taimmk/robok-bipedal/docs/images/addition/111.png

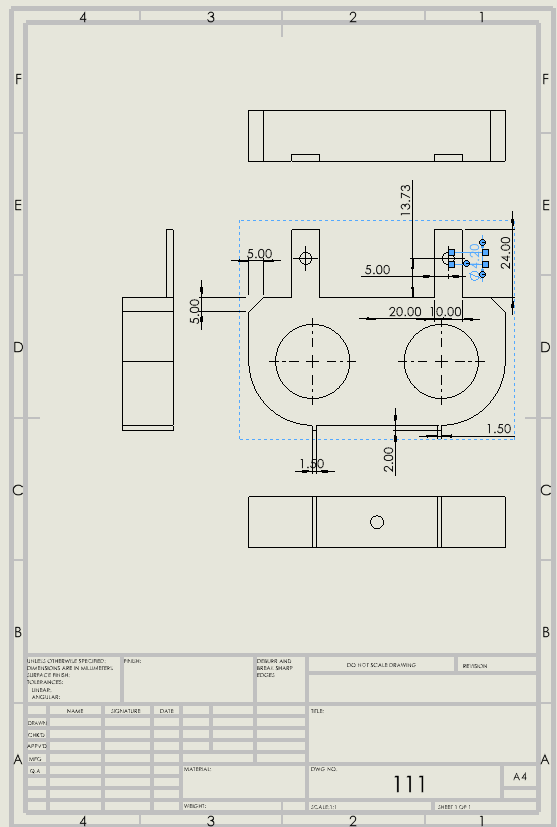
docs/images/addition/111.png
