taimmk/robok-bipedal/docs/images/addition/222.png

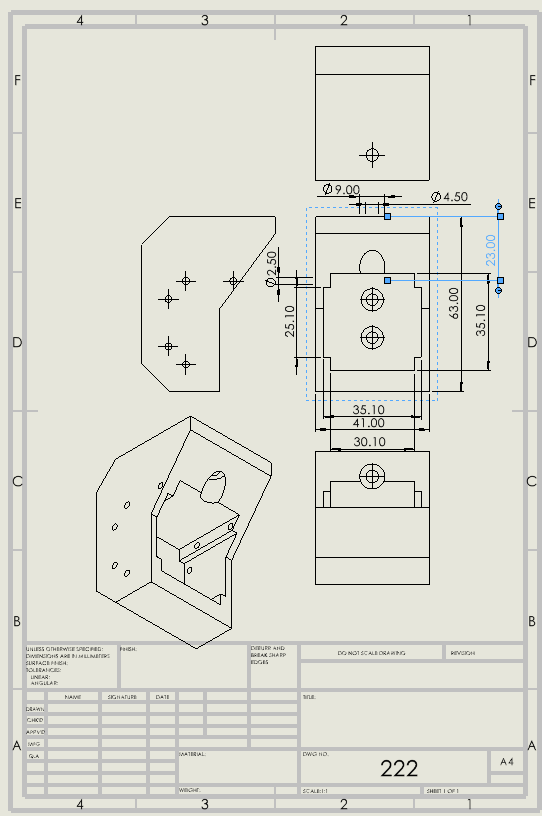
docs/images/addition/222.png
