taimmk/robok-bipedal/docs/images/addition/333.png

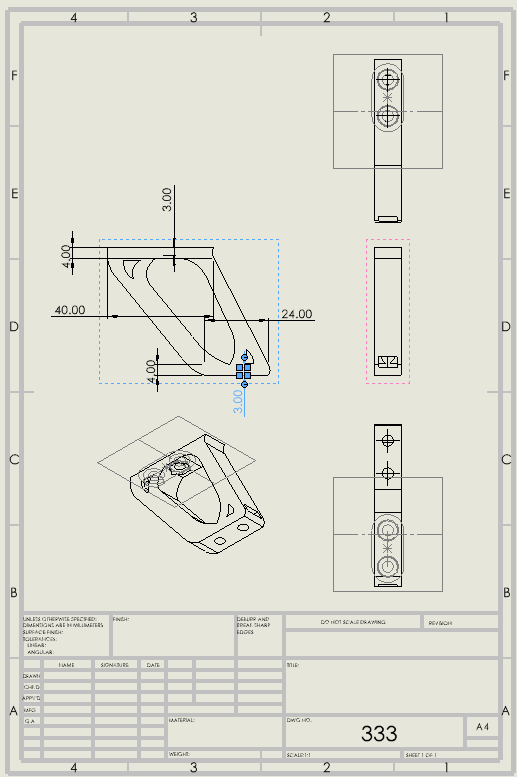
docs/images/addition/333.png
