taimmk/robok-bipedal/docs/images/addition/444.png

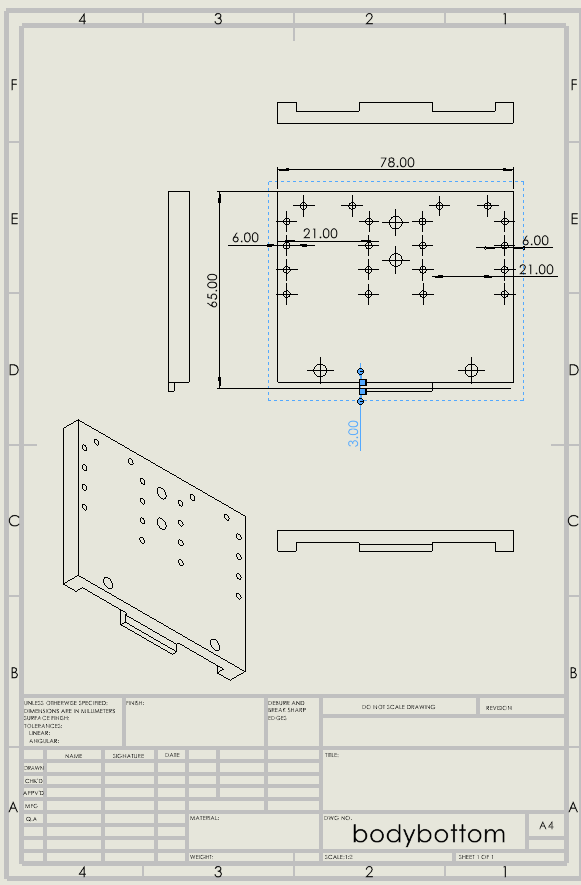
docs/images/addition/444.png
