taimmk/robok-bipedal/docs/images/addition/555.png

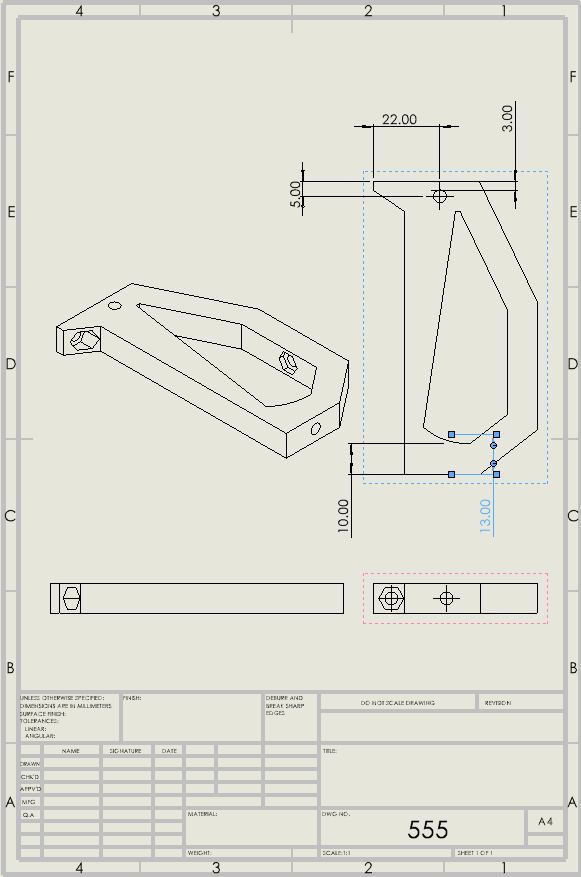
docs/images/addition/555.png
