taimmk/robok-bipedal/docs/images/addition/foot1.png

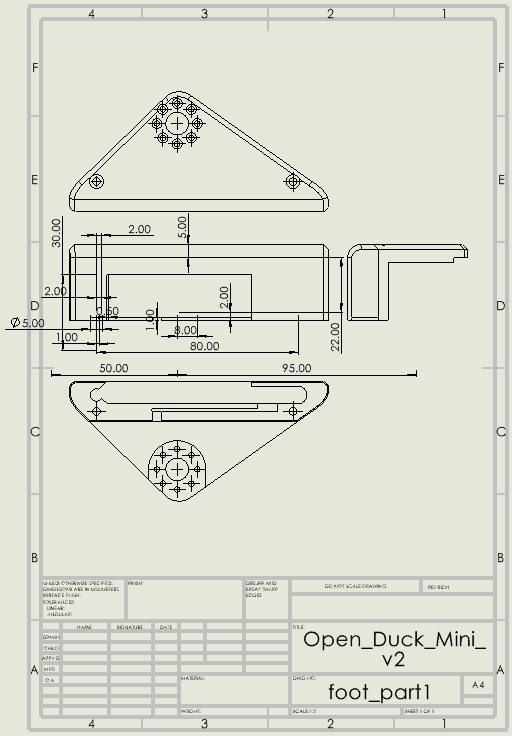
docs/images/addition/foot1.png
