taimmk/robok-bipedal/docs/images/addition/foot2.png

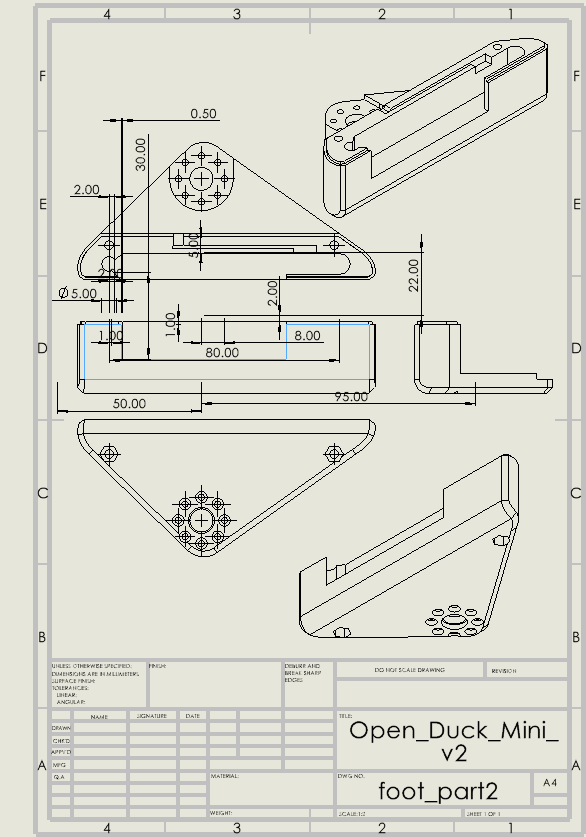
docs/images/addition/foot2.png
