taimmk/robok-bipedal/docs/images/addition/footbot.png

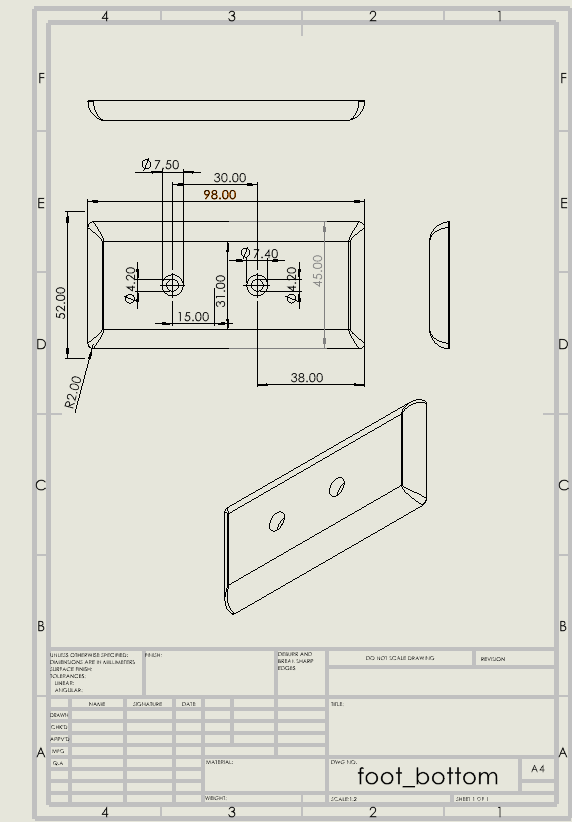
docs/images/addition/footbot.png
