taimmk/robok-bipedal/docs/images/addition/hipallined.png

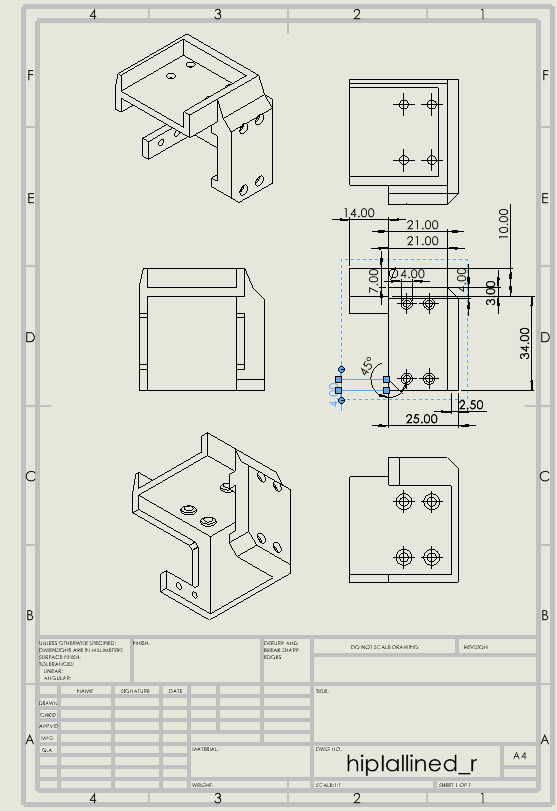
docs/images/addition/hipallined.png
