taimmk/robok-bipedal/docs/images/addition/hipII.png

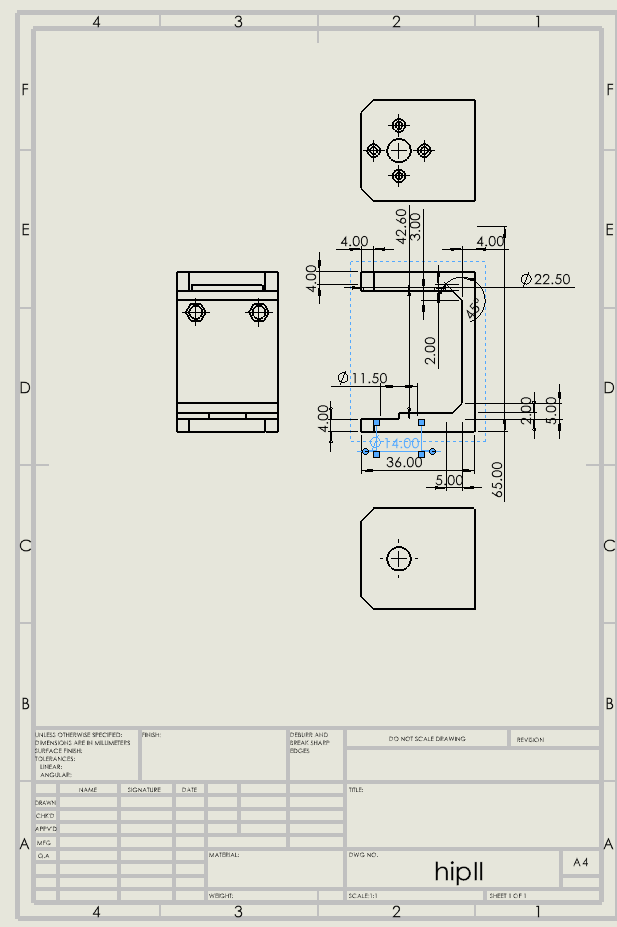
docs/images/addition/hipII.png
