taimmk/robok-bipedal/docs/images/addition/hiproll.png

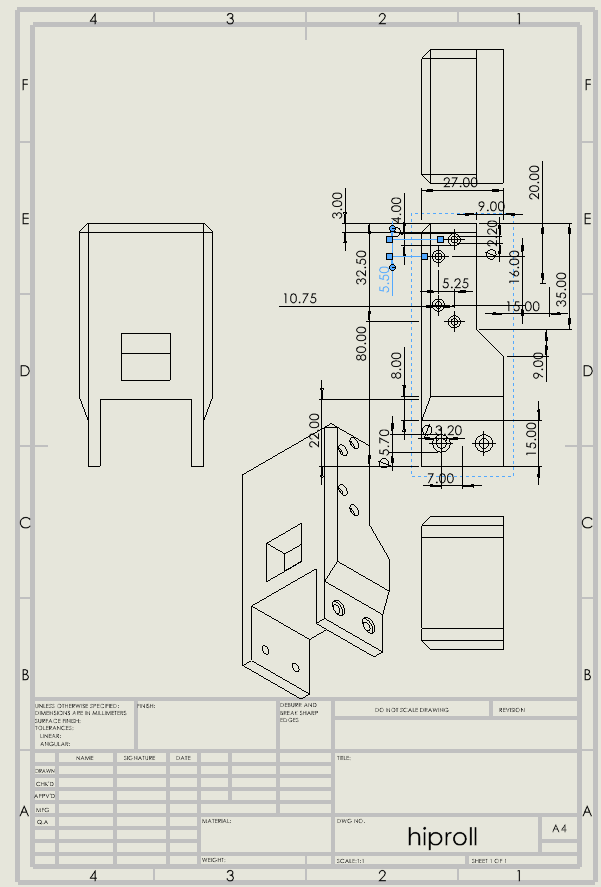
docs/images/addition/hiproll.png
