taimmk/robok-bipedal/docs/images/addition/link.png

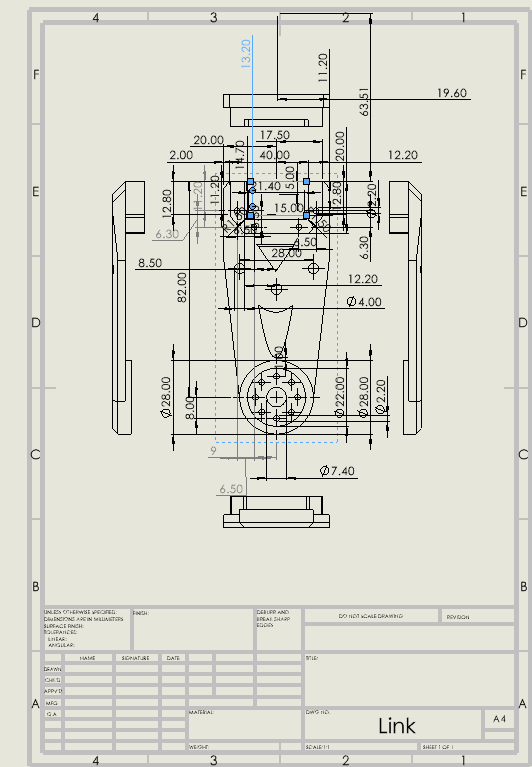
docs/images/addition/link.png
