taimmk/robok-bipedal/docs/images/addition/linkII.png

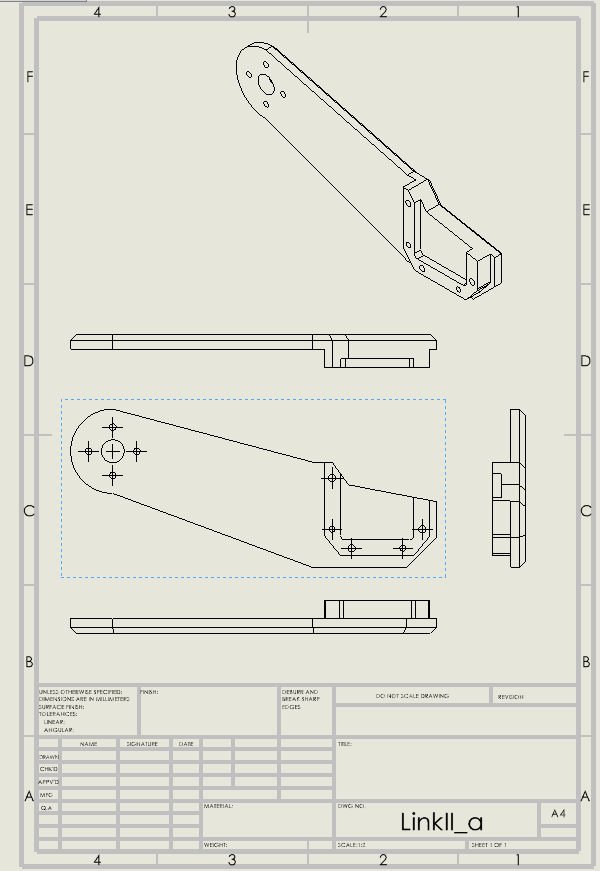
docs/images/addition/linkII.png
