taimmk/robok-bipedal/docs/images/addition/nick.png

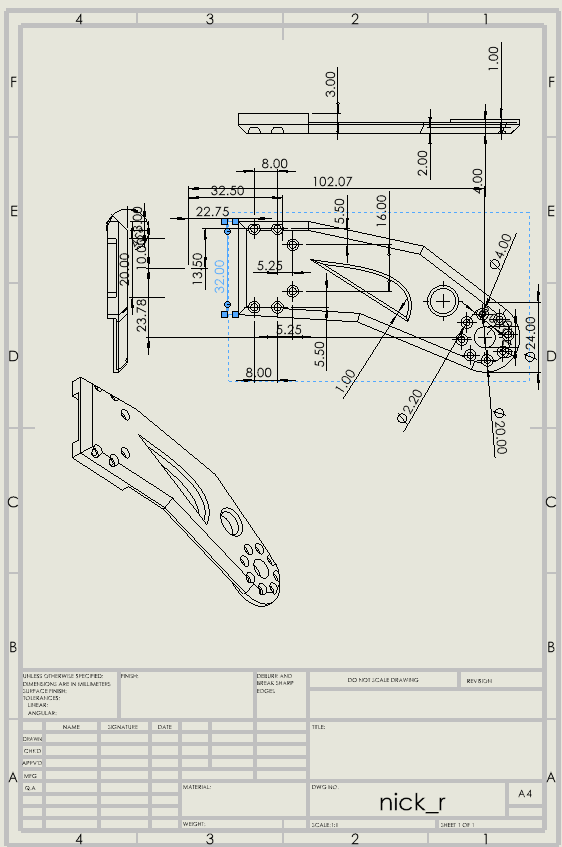
docs/images/addition/nick.png
