taimmk/robok-bipedal/docs/images/addition/nickroll.png

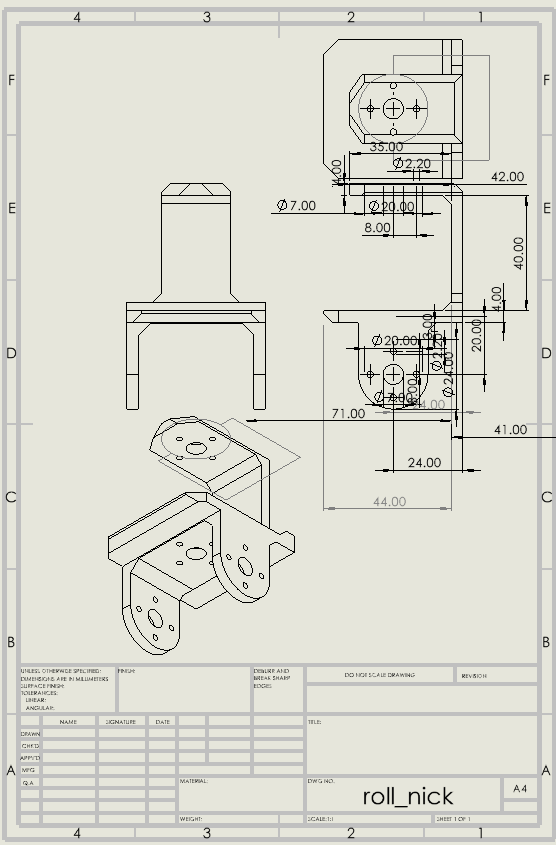
docs/images/addition/nickroll.png
