taimmk/robok-bipedal/docs/images/addition/rollertop.png

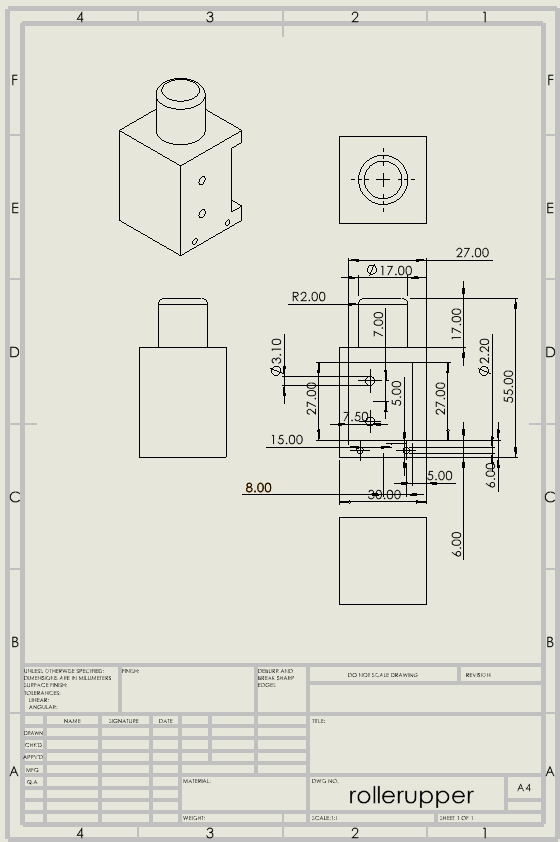
docs/images/addition/rollertop.png
