taimmk/robok-bipedal/docs/images/ANSYS/foot_modal.png

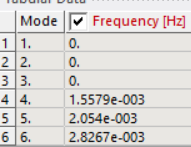
docs/images/ANSYS/foot_modal.png
