taimmk/robok-bipedal/docs/images/ANSYS/foot_optemize.png

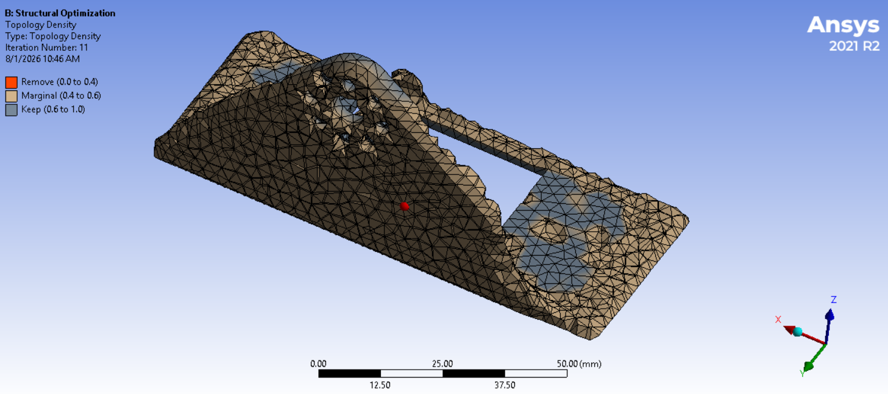
docs/images/ANSYS/foot_optemize.png
