taimmk/robok-bipedal/docs/images/ANSYS/foot_react.png

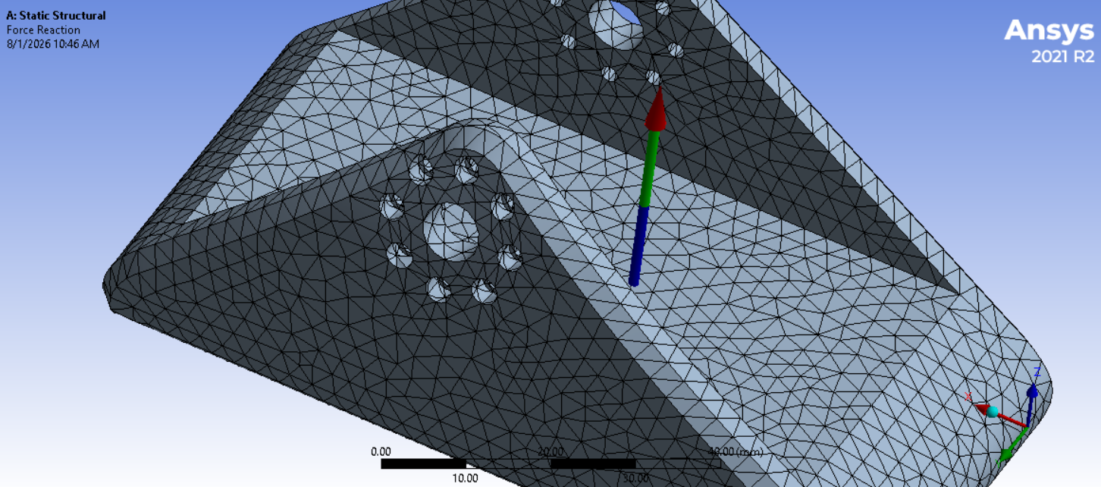
docs/images/ANSYS/foot_react.png
