taimmk/robok-bipedal/docs/images/ANSYS/foot_strain.png

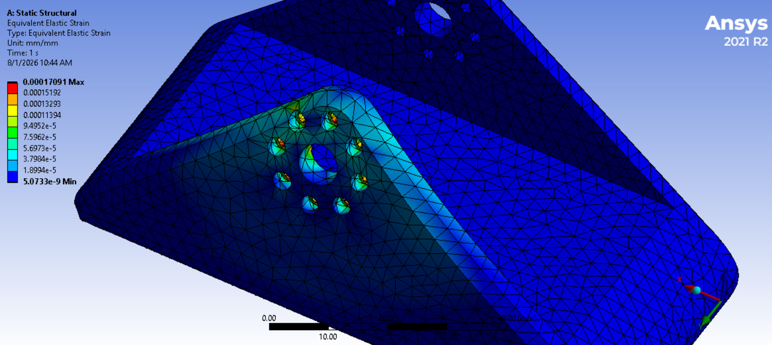
docs/images/ANSYS/foot_strain.png
