taimmk/robok-bipedal/docs/images/ANSYS/foot_totaldeformation.png

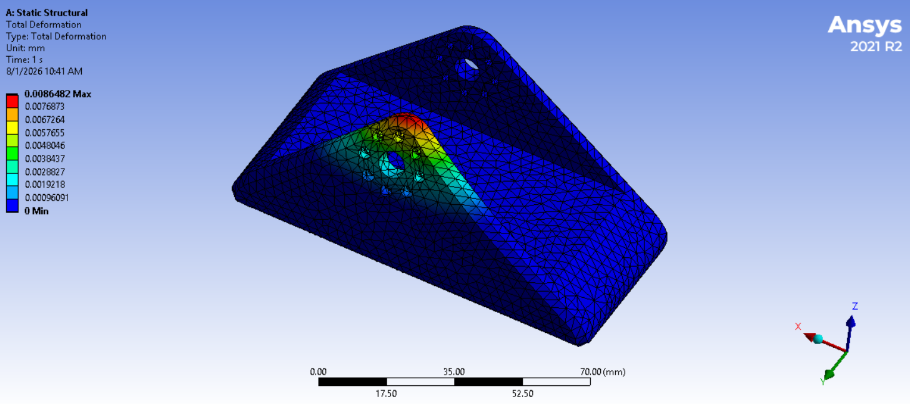
docs/images/ANSYS/foot_totaldeformation.png
