taimmk/robok-bipedal/docs/images/ANSYS/hiproll_modal.png

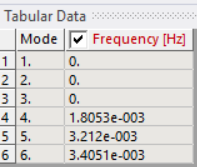
docs/images/ANSYS/hiproll_modal.png
