taimmk/robok-bipedal/docs/images/ANSYS/hiproll_optemize.png

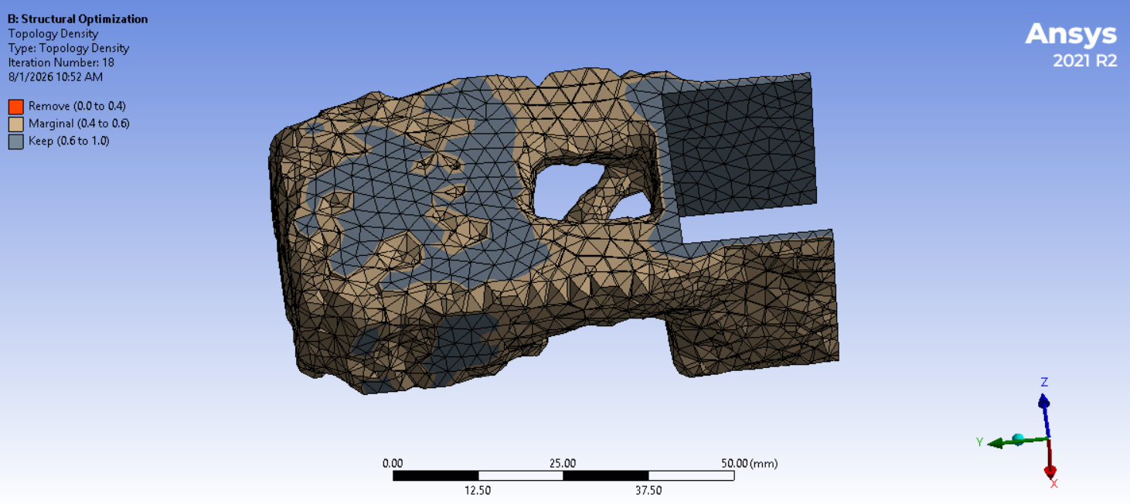
docs/images/ANSYS/hiproll_optemize.png
