taimmk/robok-bipedal/docs/images/ANSYS/hiproll_strain.png

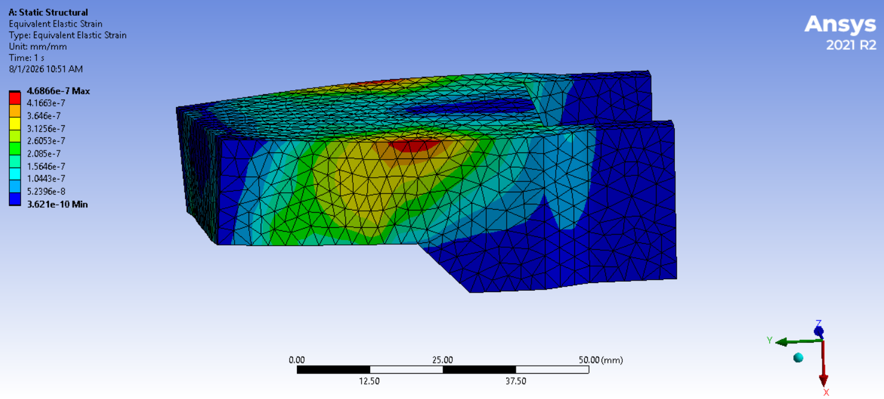
docs/images/ANSYS/hiproll_strain.png
