taimmk/robok-bipedal/docs/images/ANSYS/hiproll_totaldeformation.png

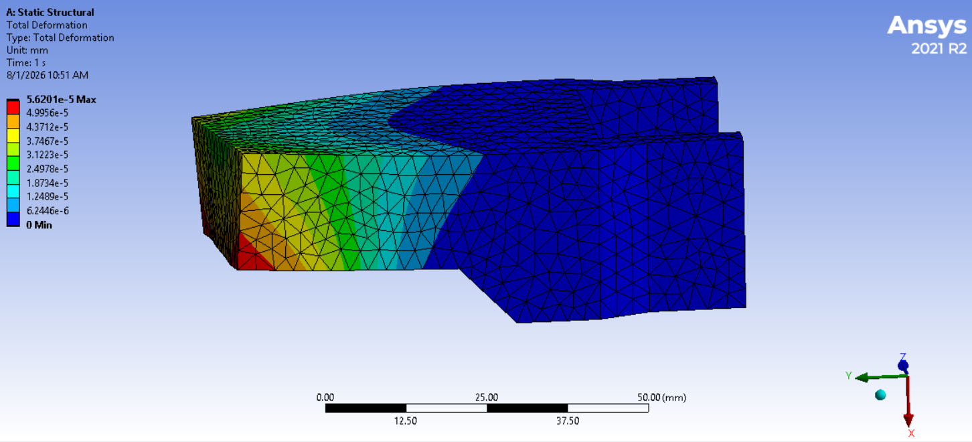
docs/images/ANSYS/hiproll_totaldeformation.png
