taimmk/robok-bipedal/docs/images/ANSYS/linki_optemize.png

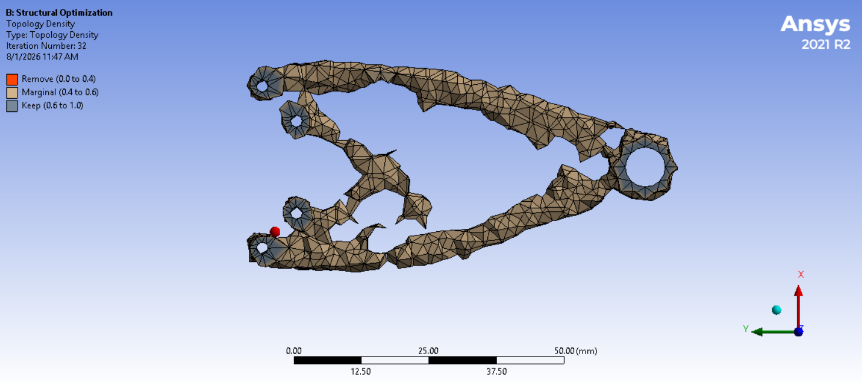
docs/images/ANSYS/linki_optemize.png
