taimmk/robok-bipedal/docs/images/ANSYS/linki_react.png

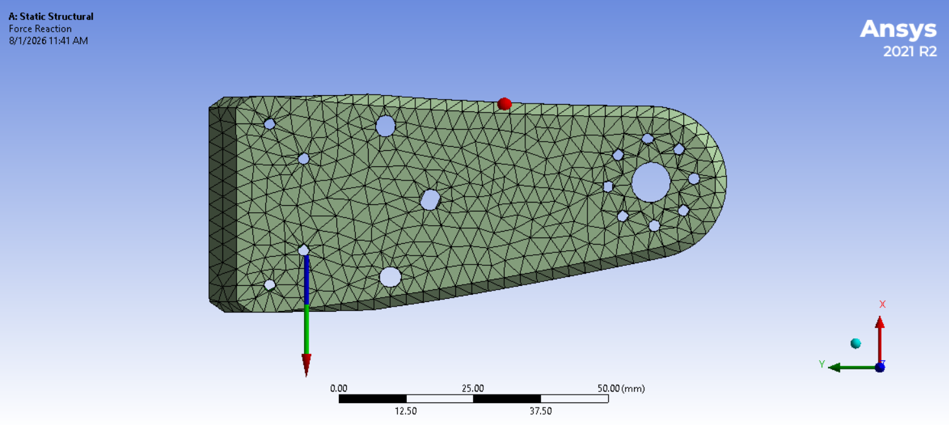
docs/images/ANSYS/linki_react.png
