taimmk/robok-bipedal/docs/images/ANSYS/linki_strain.png

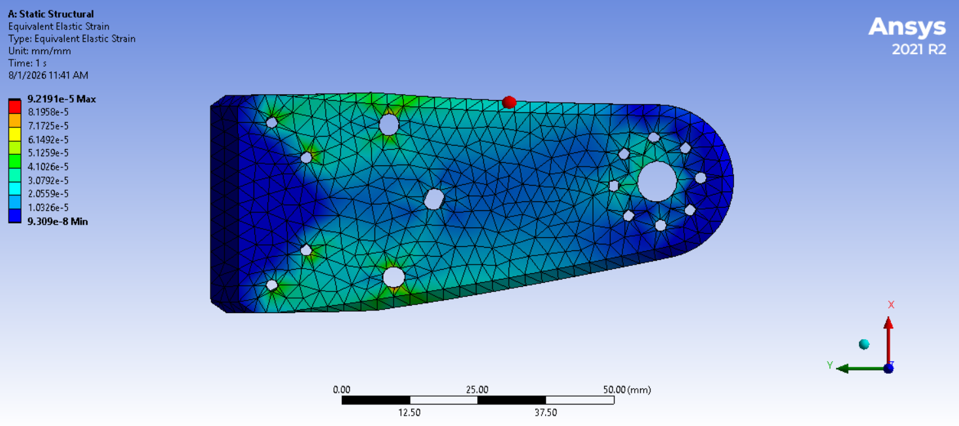
docs/images/ANSYS/linki_strain.png
