taimmk/robok-bipedal/docs/images/ANSYS/linki_totaldeformation.png

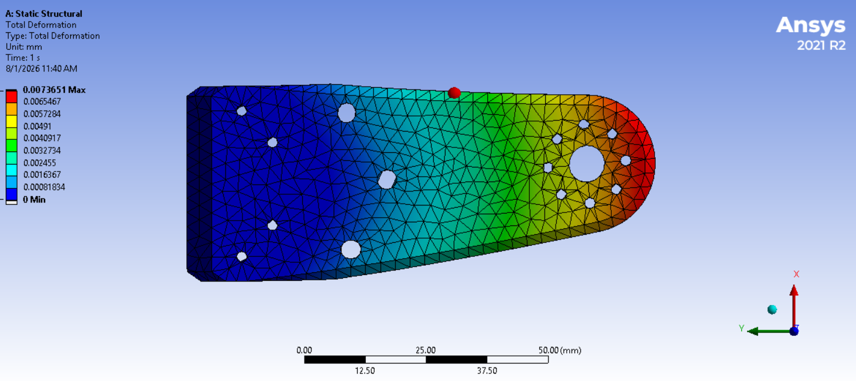
docs/images/ANSYS/linki_totaldeformation.png
