taimmk/robok-bipedal/docs/images/ANSYS/linkii_optemize.png

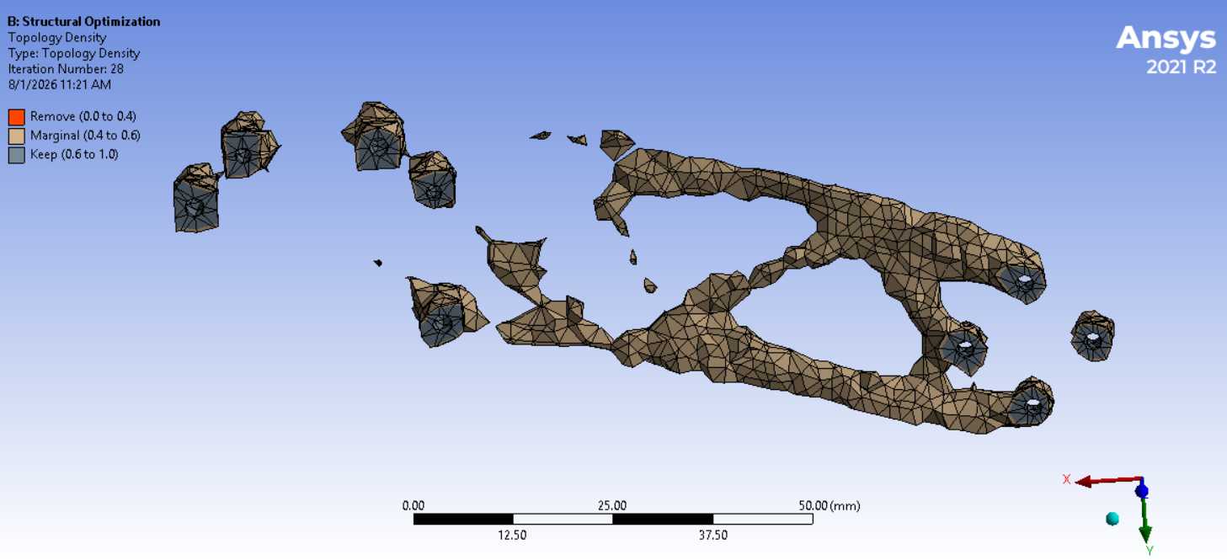
docs/images/ANSYS/linkii_optemize.png
