taimmk/robok-bipedal/docs/images/ANSYS/linkii_react.png

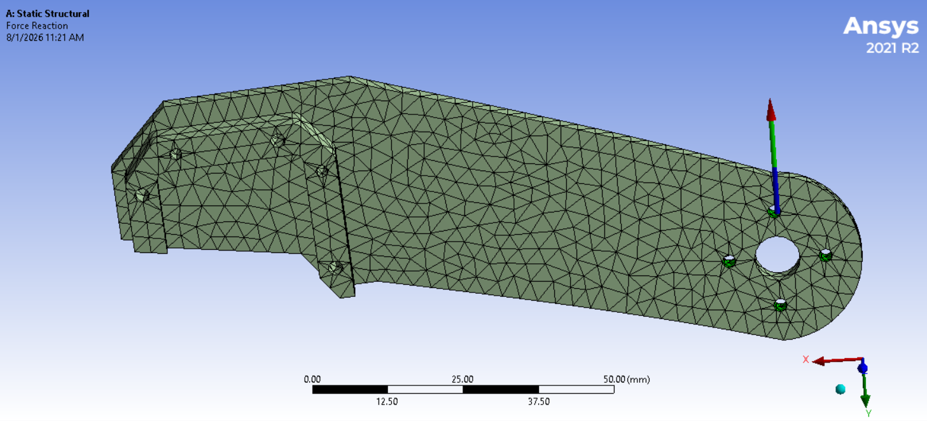
docs/images/ANSYS/linkii_react.png
