taimmk/robok-bipedal/docs/images/ANSYS/linkii_strain.png

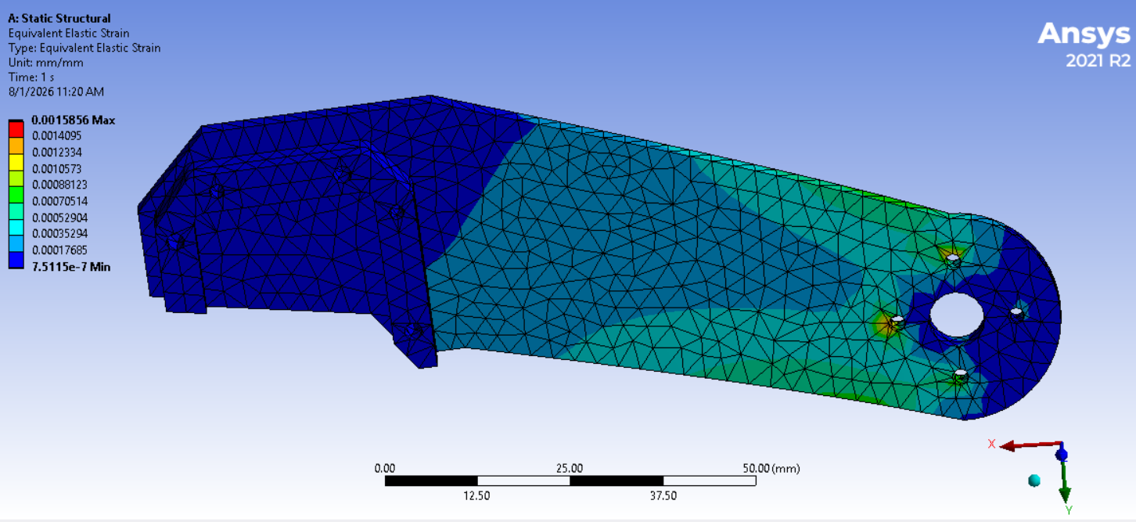
docs/images/ANSYS/linkii_strain.png
