taimmk/robok-bipedal/docs/images/ANSYS/linkii_totaldeformation.png

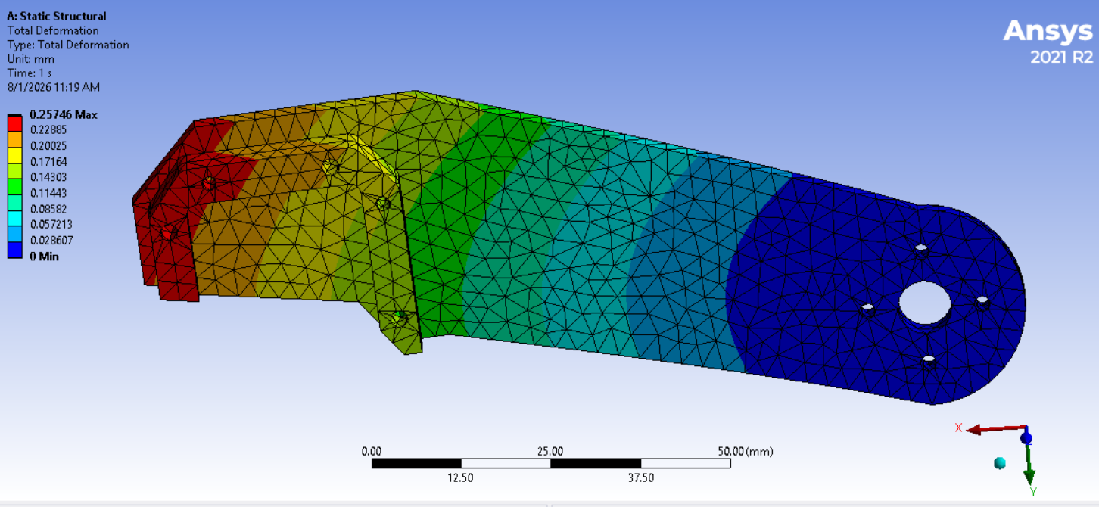
docs/images/ANSYS/linkii_totaldeformation.png
