taimmk/robok-bipedal/docs/images/ANSYS/nick_optemize.png

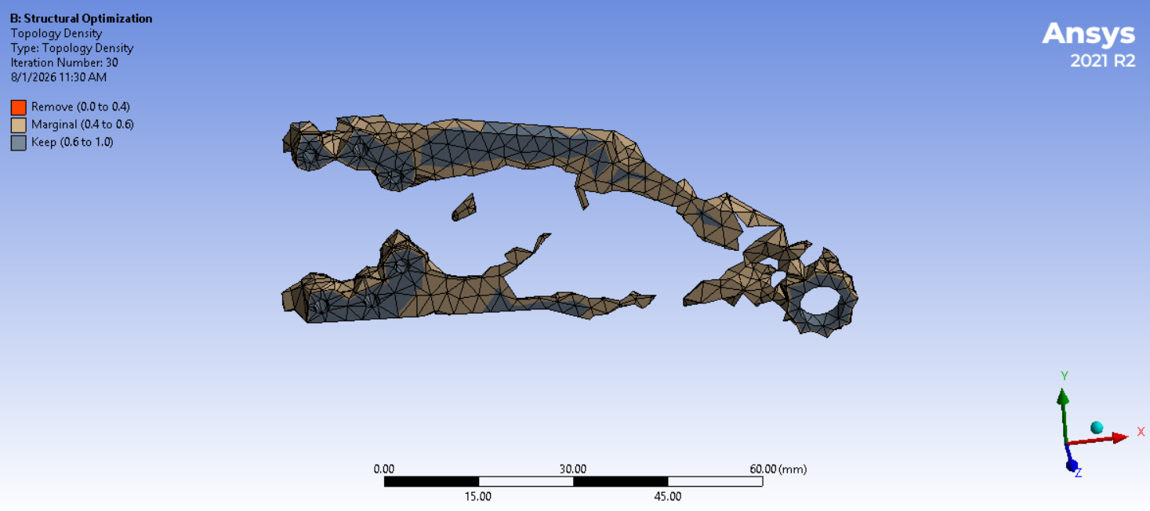
docs/images/ANSYS/nick_optemize.png
