taimmk/robok-bipedal/docs/images/ANSYS/nick_react.png

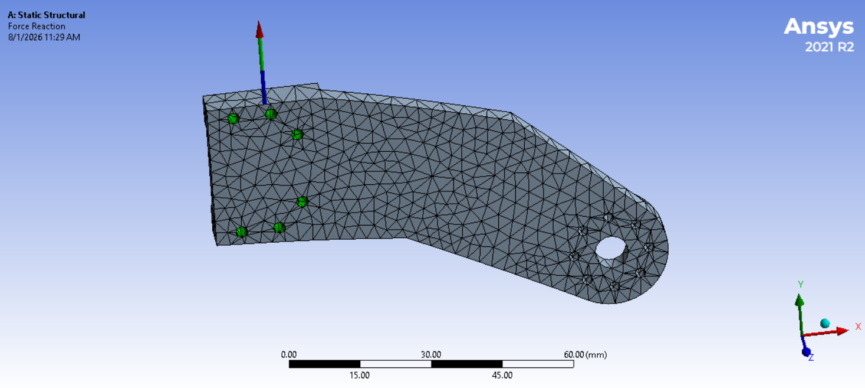
docs/images/ANSYS/nick_react.png
