taimmk/robok-bipedal/docs/images/ANSYS/nick_strain.png

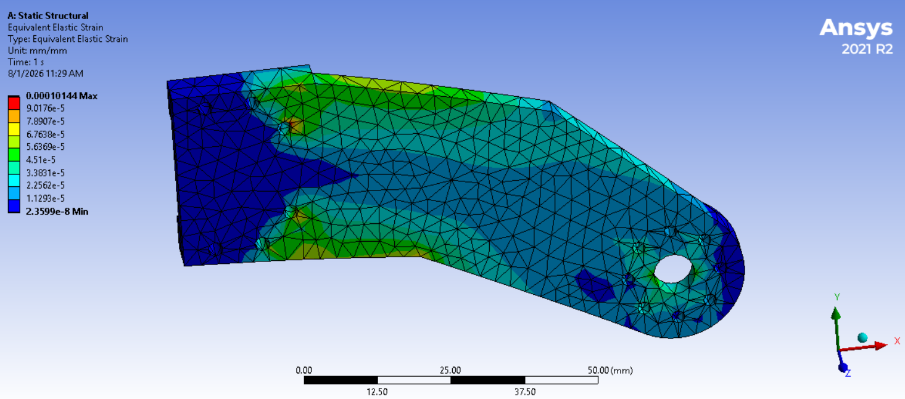
docs/images/ANSYS/nick_strain.png
