taimmk/robok-bipedal/docs/images/ANSYS/nick_totaldeformation.png

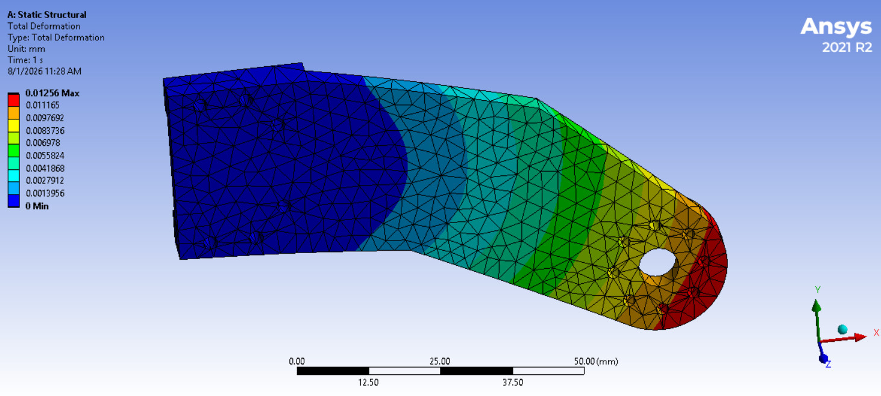
docs/images/ANSYS/nick_totaldeformation.png
