taimmk/robok-bipedal/docs/images/configuration.png

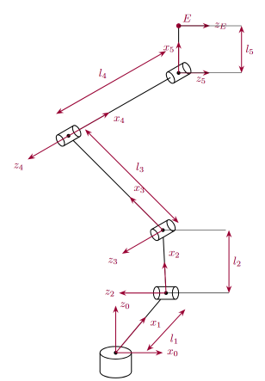
docs/images/configuration.png
