taimmk/robok-bipedal/docs/images/fkmat.png

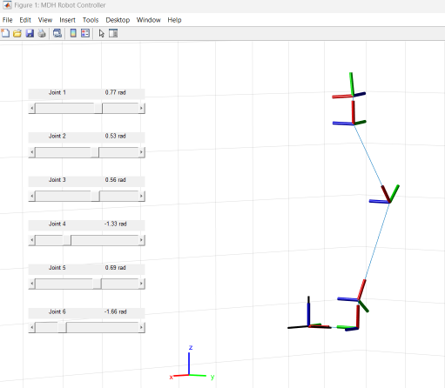
docs/images/fkmat.png
