taimmk/robok-bipedal/docs/images/funcitonsanswhy.png

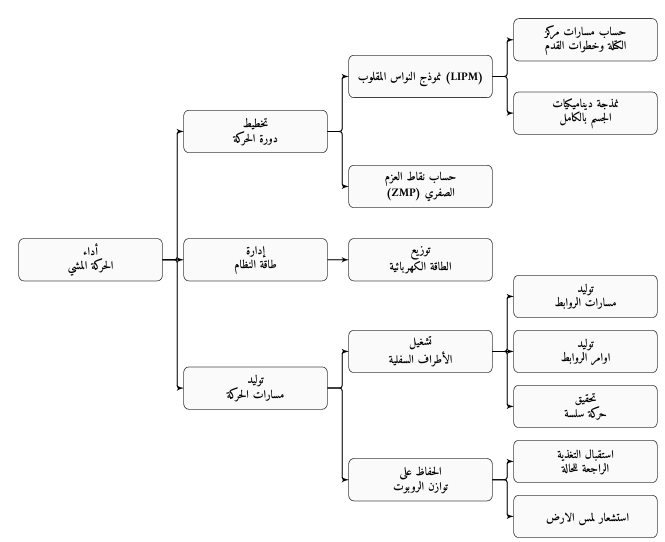
docs/images/funcitonsanswhy.png
