taimmk/robok-bipedal/docs/images/hornsdiagrams.png

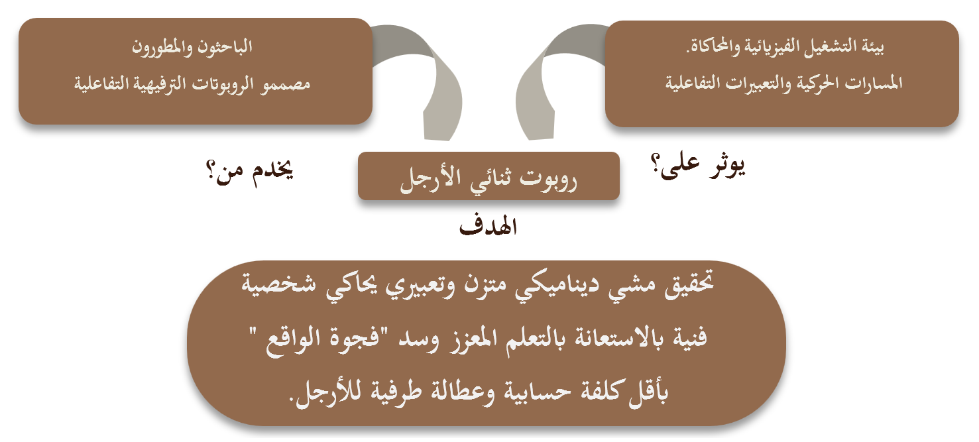
docs/images/hornsdiagrams.png
