taimmk/robok-bipedal/docs/images/inputoutput01.png

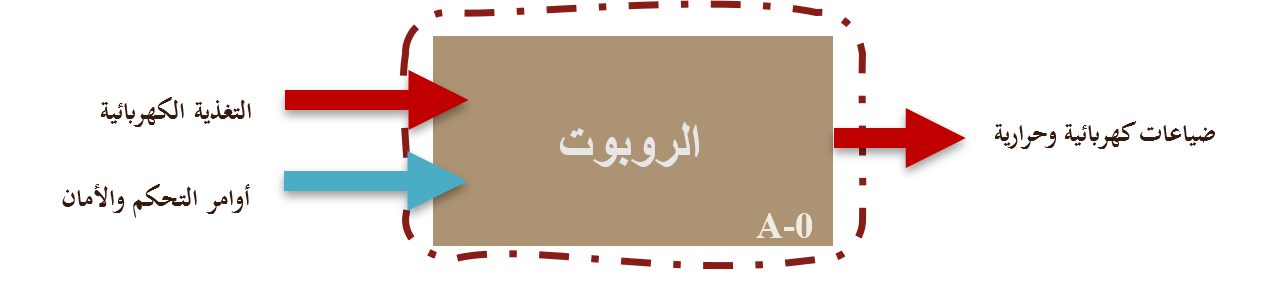
docs/images/inputoutput01.png
