taimmk/robok-bipedal/docs/images/invkin.png

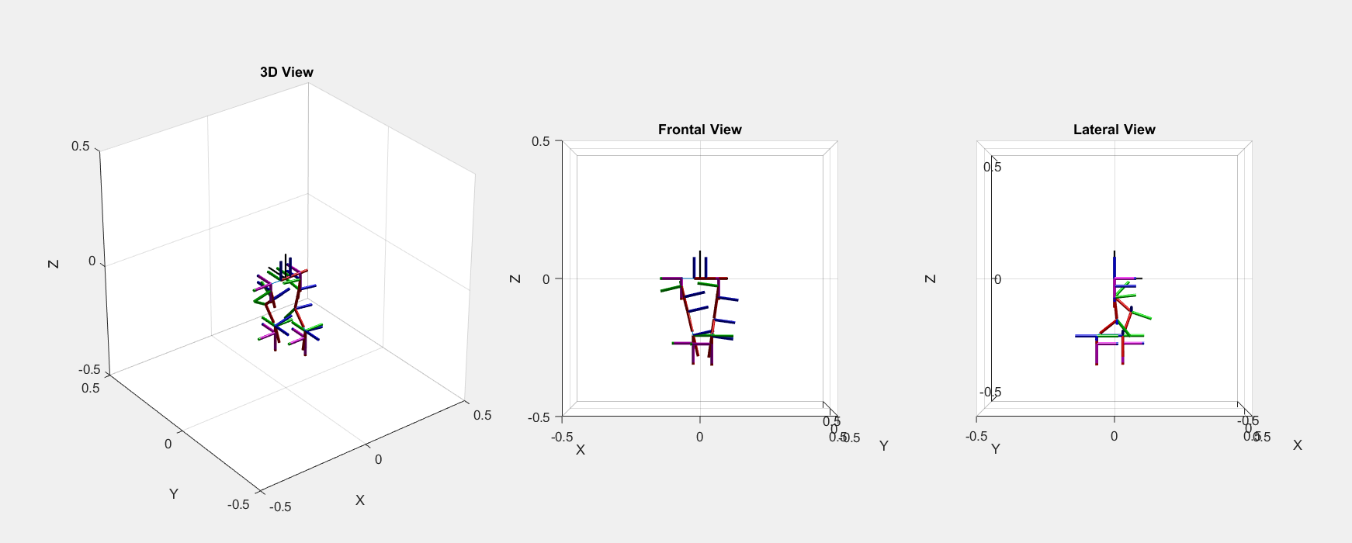
docs/images/invkin.png
