taimmk/robok-bipedal/docs/images/joint1.png

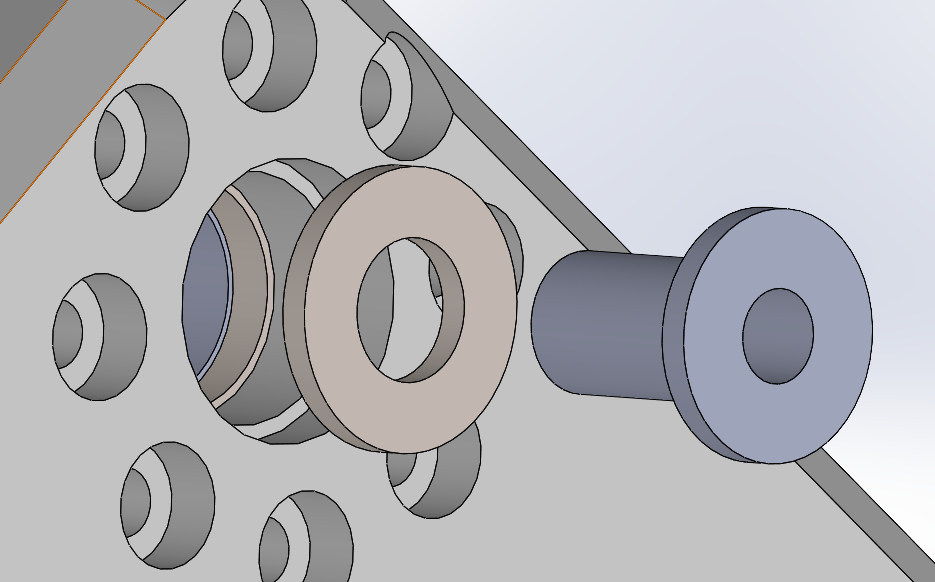
docs/images/joint1.png
