taimmk/robok-bipedal/docs/images/joint2.png

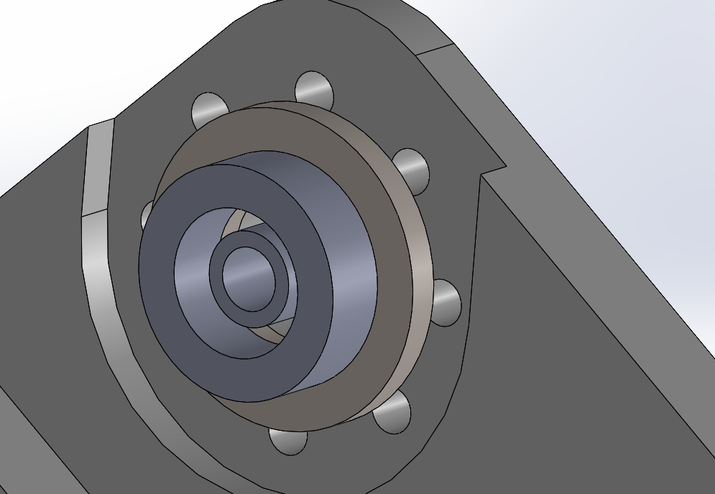
docs/images/joint2.png
