taimmk/robok-bipedal/docs/images/jointax.png

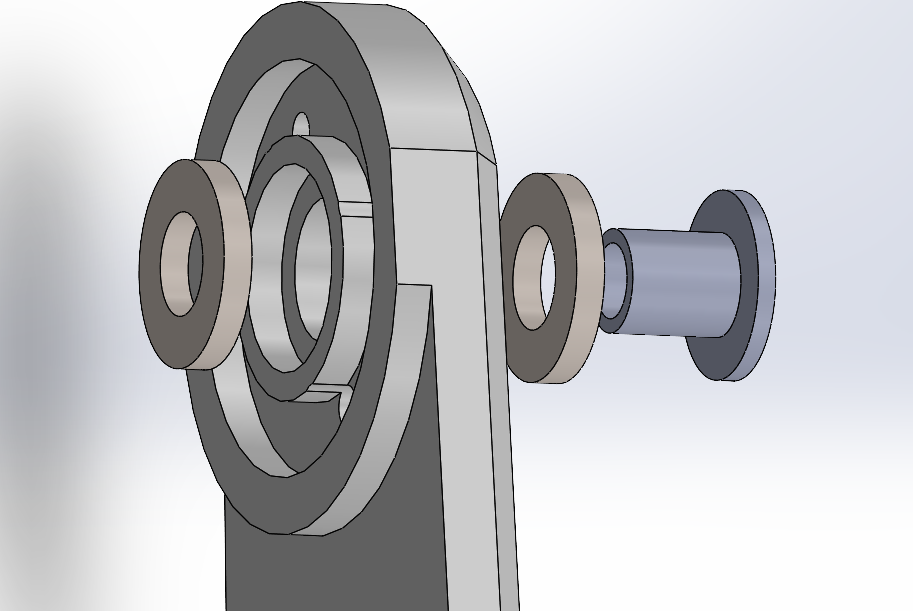
docs/images/jointax.png
