taimmk/robok-bipedal/docs/images/LIPM.png

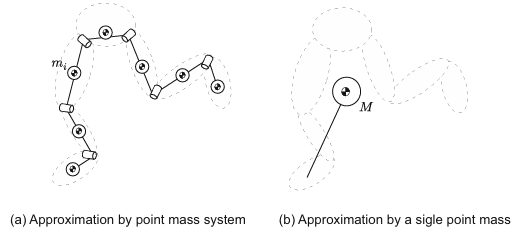
docs/images/LIPM.png
