taimmk/robok-bipedal/docs/images/lipmapp.png

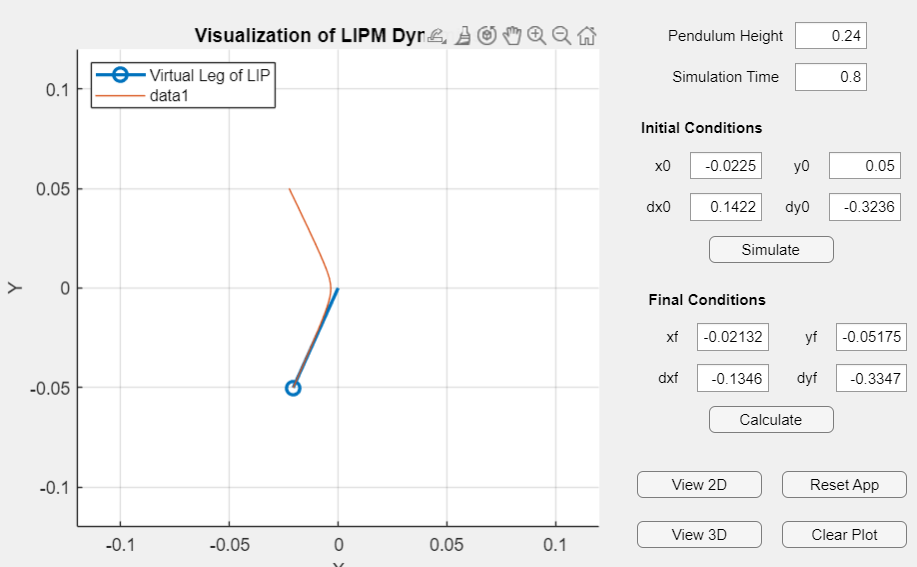
docs/images/lipmapp.png
