taimmk/robok-bipedal/docs/images/lipmoutput.png

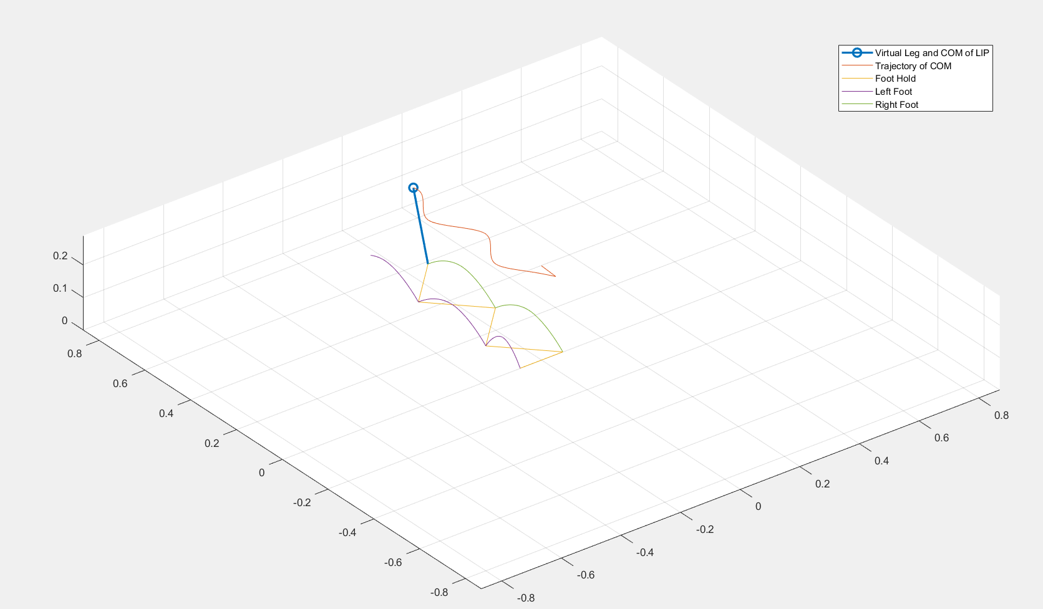
docs/images/lipmoutput.png
