taimmk/robok-bipedal/docs/images/matlabdiagram.png

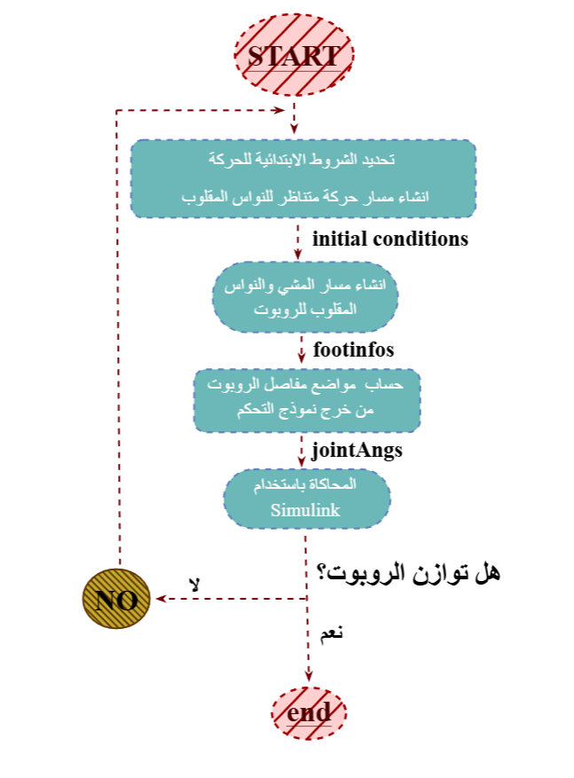
docs/images/matlabdiagram.png
