taimmk/robok-bipedal/docs/images/mpc.jpg

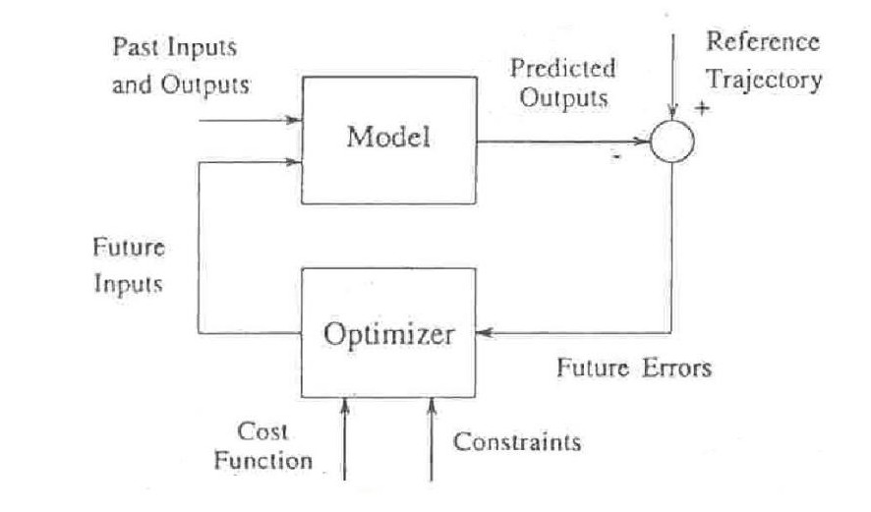
docs/images/mpc.jpg
