taimmk/robok-bipedal/docs/images/orbital_energy.png

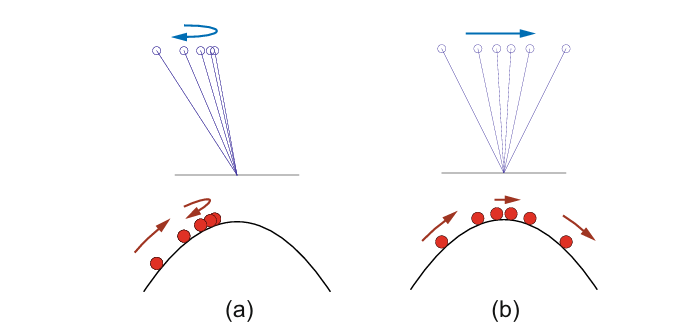
docs/images/orbital_energy.png
