taimmk/robok-bipedal/docs/images/outaffect.png

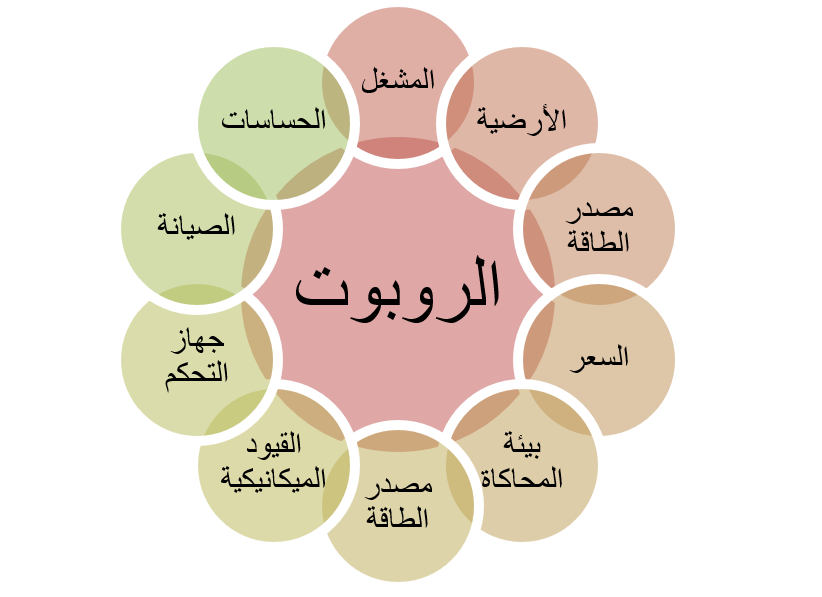
docs/images/outaffect.png
