taimmk/robok-bipedal/docs/images/PCB/communication_2d.png

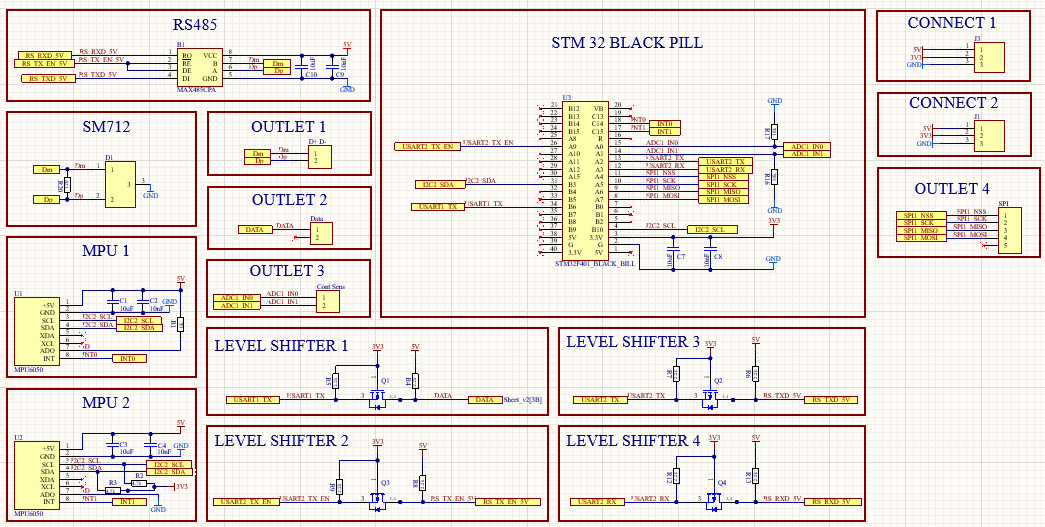
docs/images/PCB/communication_2d.png
