taimmk/robok-bipedal/docs/images/PCB/communication_3d.png

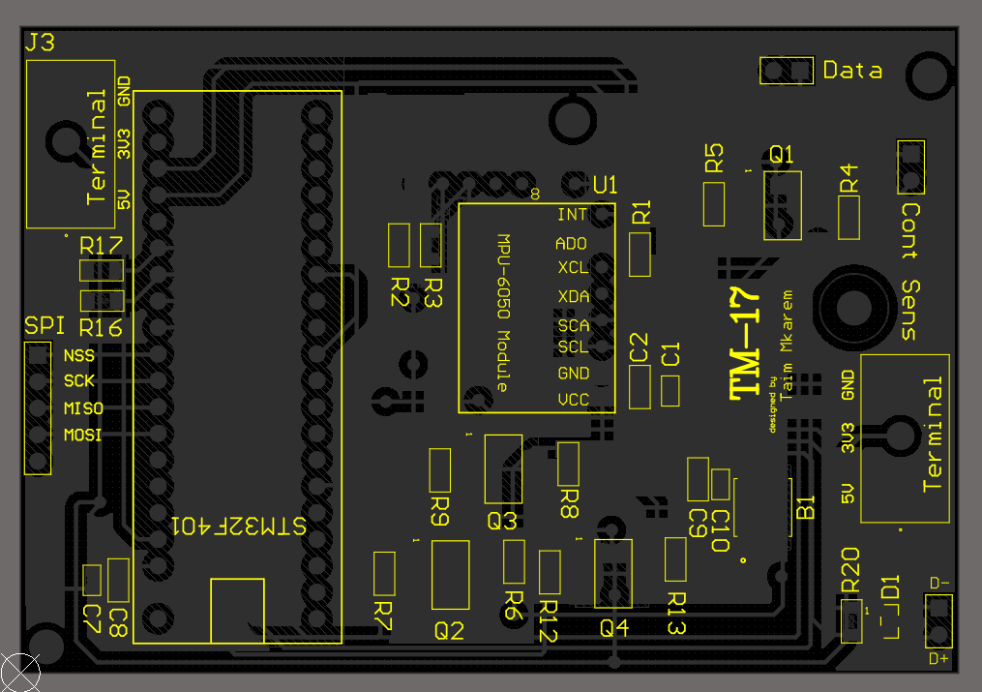
docs/images/PCB/communication_3d.png
