taimmk/robok-bipedal/docs/images/PCB/Gemini_Generated_Image_nam9vcnam9vcnam9.png

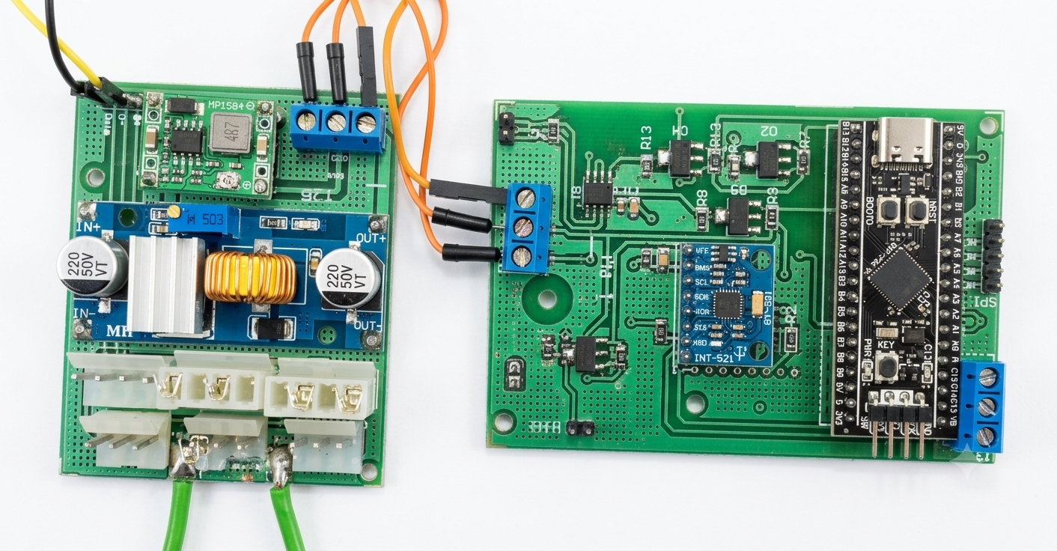
docs/images/PCB/Gemini_Generated_Image_nam9vcnam9vcnam9.png
