taimmk/robok-bipedal/docs/images/PCB/power_2d.png

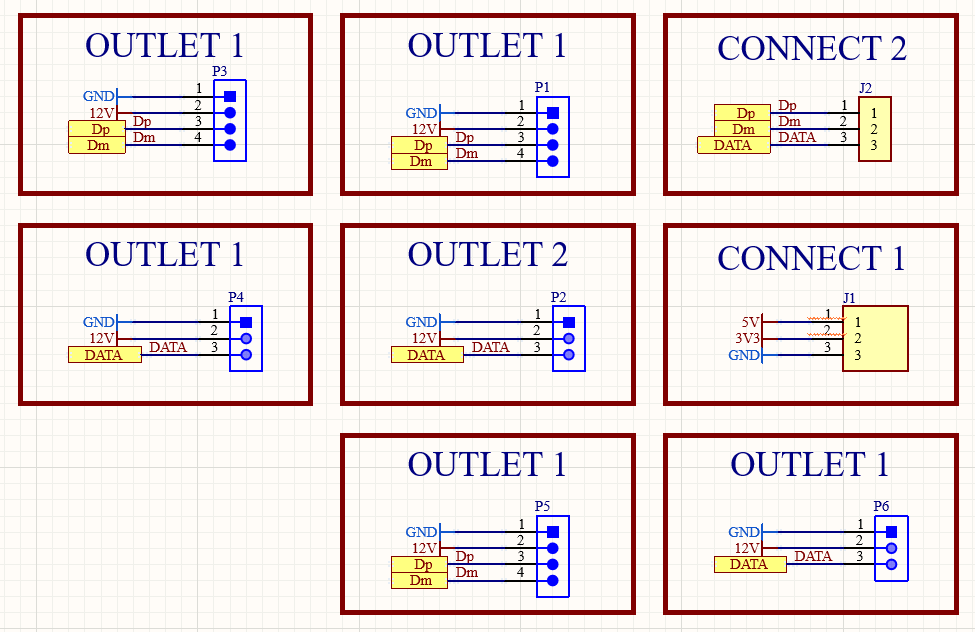
docs/images/PCB/power_2d.png
