taimmk/robok-bipedal/docs/images/PCB/power_3d.png

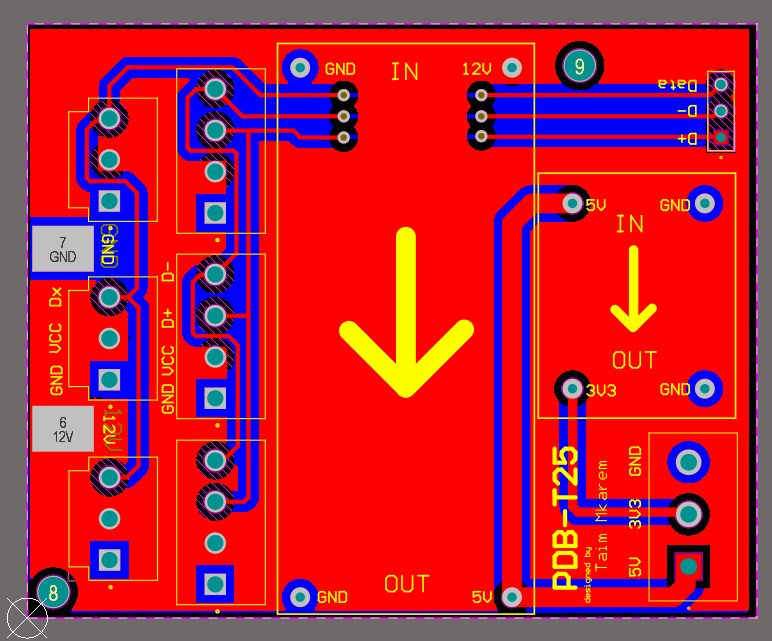
docs/images/PCB/power_3d.png
