taimmk/robok-bipedal/docs/images/PCB/real.jpg

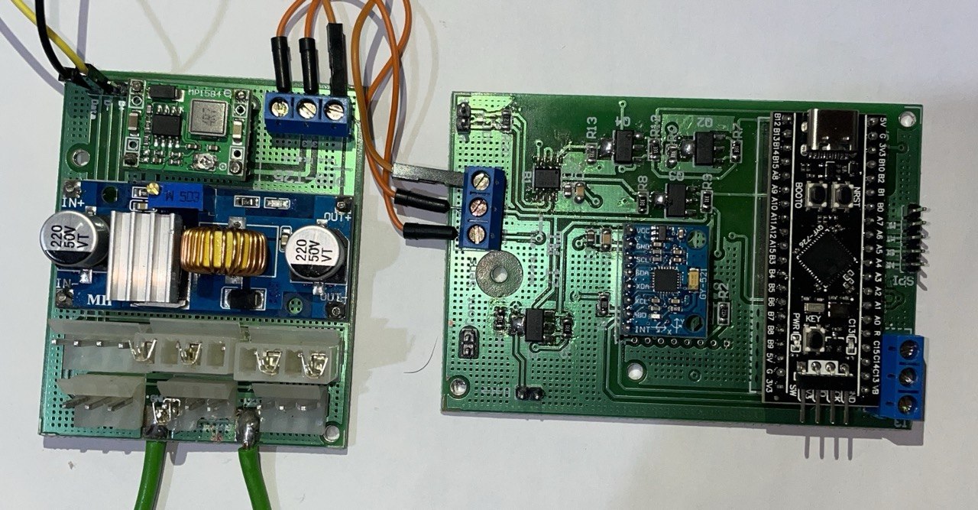
docs/images/PCB/real.jpg
