taimmk/robok-bipedal/docs/images/real.png

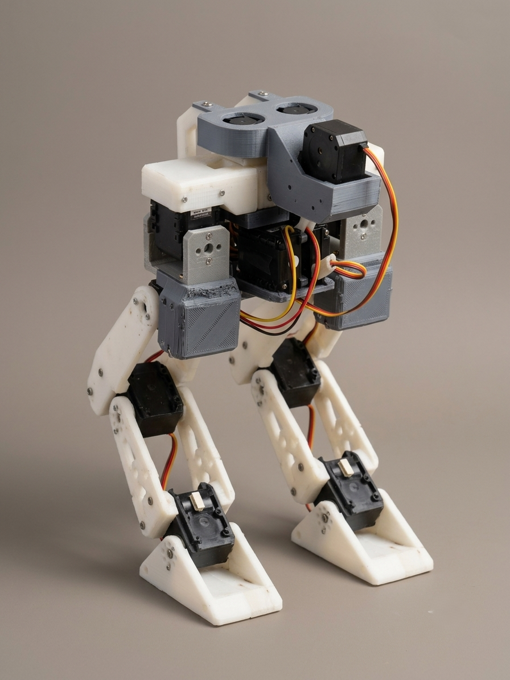
docs/images/real.png
