taimmk/robok-bipedal/docs/images/realside.png

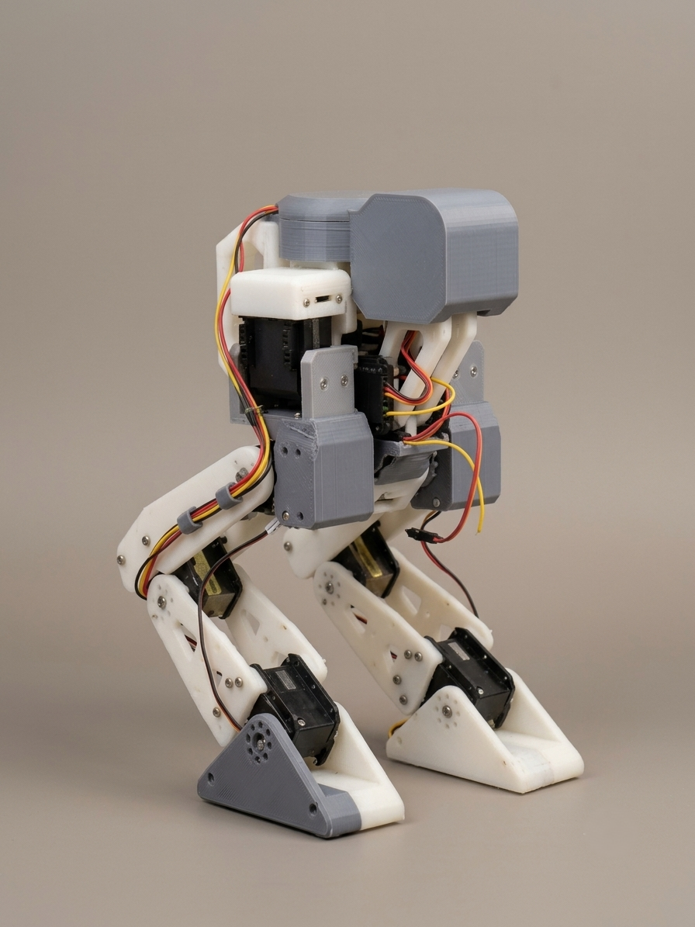
docs/images/realside.png
