taimmk/robok-bipedal/docs/images/rl/feetairtime.png

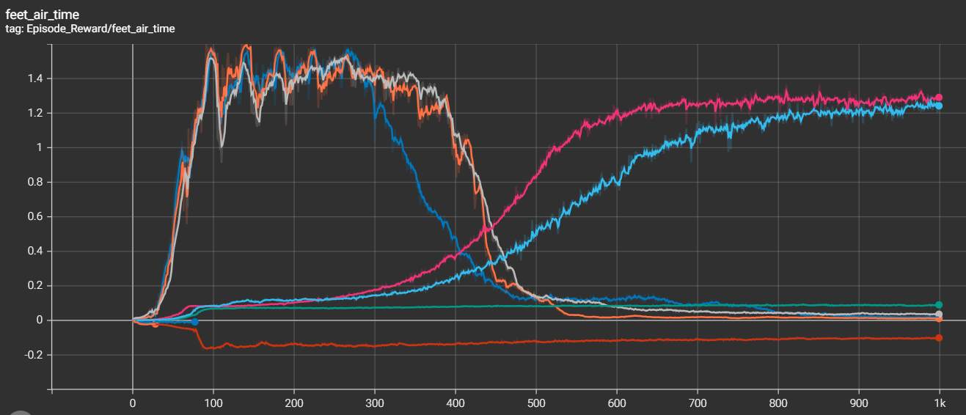
docs/images/rl/feetairtime.png
