taimmk/robok-bipedal/docs/images/rl/learningrate.png

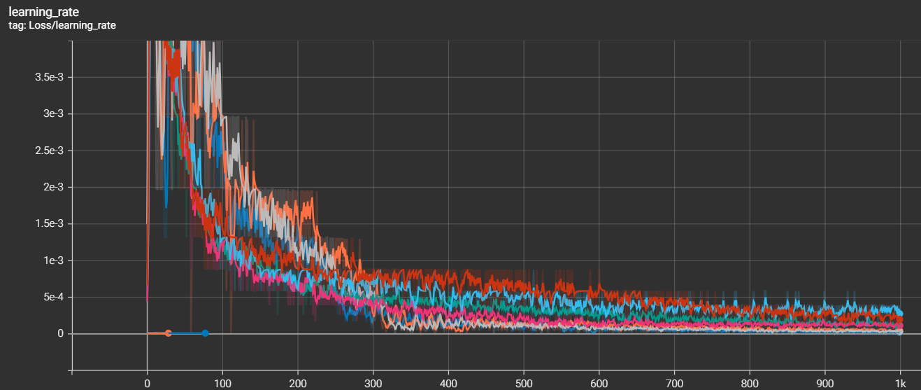
docs/images/rl/learningrate.png
