taimmk/robok-bipedal/docs/images/rl/meanepisodelength.png

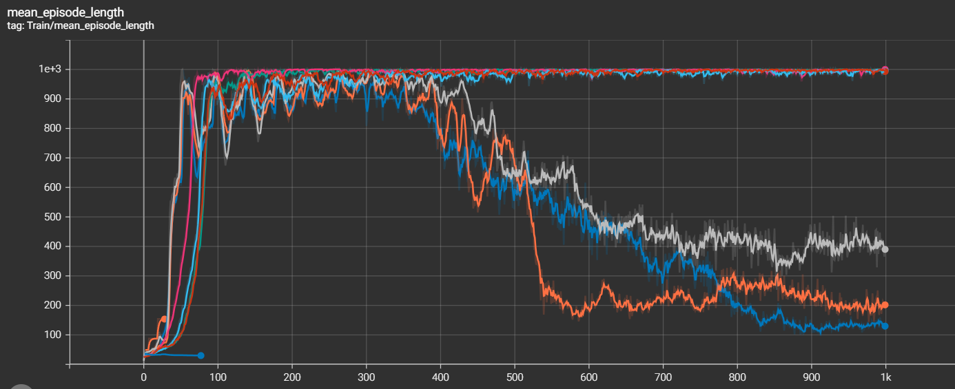
docs/images/rl/meanepisodelength.png
