taimmk/robok-bipedal/docs/images/rl/meanreward.png

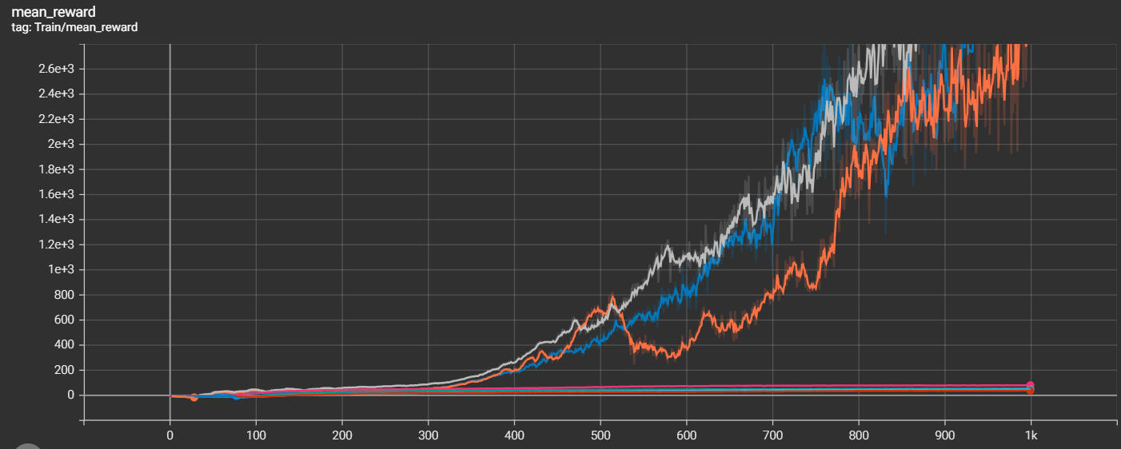
docs/images/rl/meanreward.png
