taimmk/robok-bipedal/docs/images/rl/meanstd.png

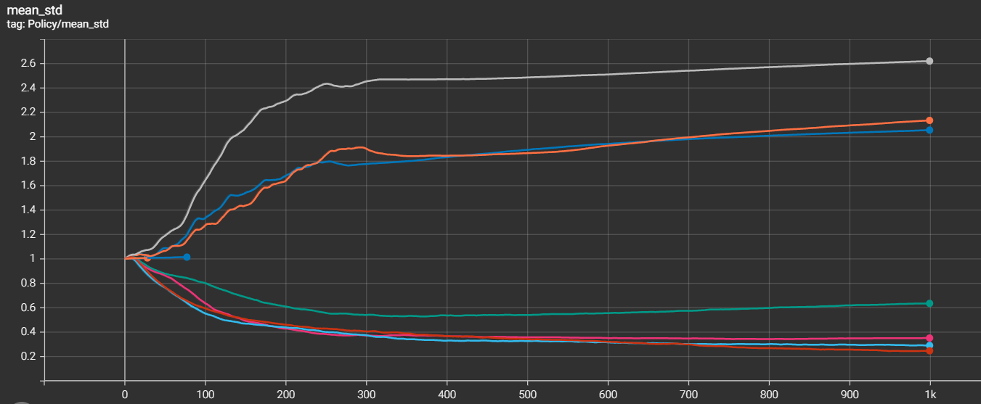
docs/images/rl/meanstd.png
