taimmk/robok-bipedal/docs/images/rl/sucessrate.png

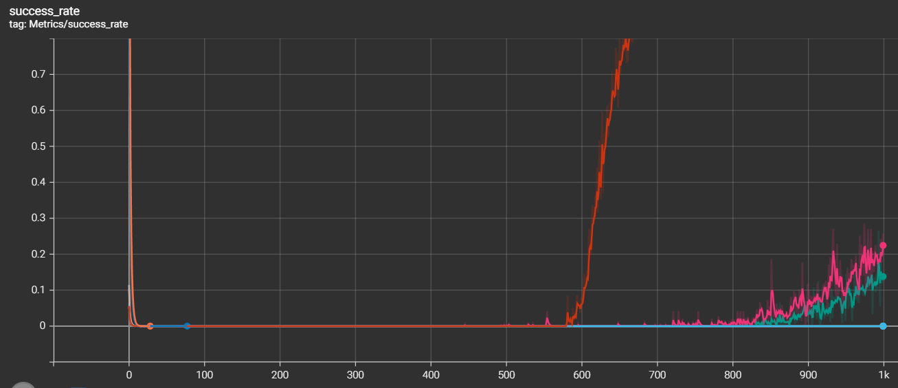
docs/images/rl/sucessrate.png
