taimmk/robok-bipedal/docs/images/rlrsl.png

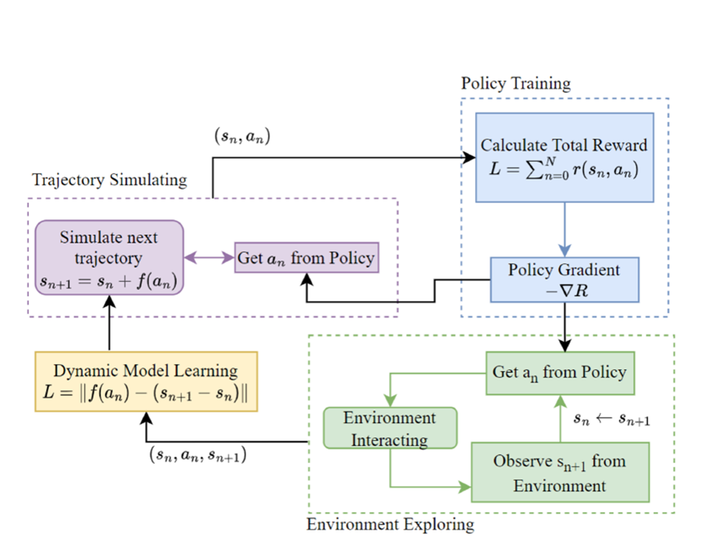
docs/images/rlrsl.png
