taimmk/robok-bipedal/docs/images/robokfront.png

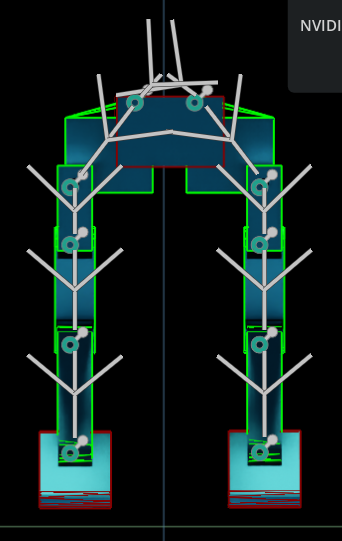
docs/images/robokfront.png
