taimmk/robok-bipedal/docs/images/robokpre.png

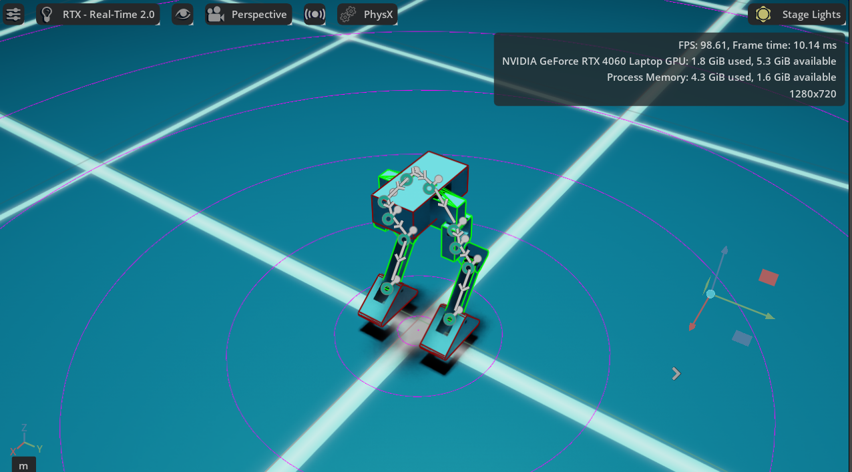
docs/images/robokpre.png
