taimmk/robok-bipedal/docs/images/robokright.png

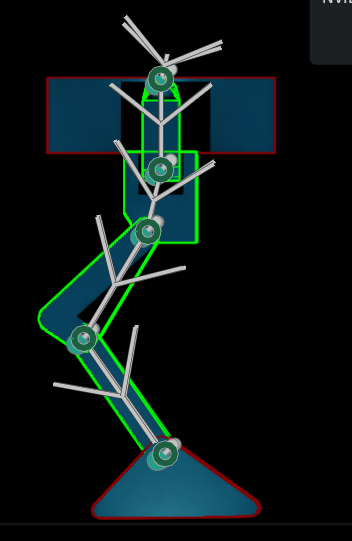
docs/images/robokright.png
