taimmk/robok-bipedal/docs/images/rslrl.png

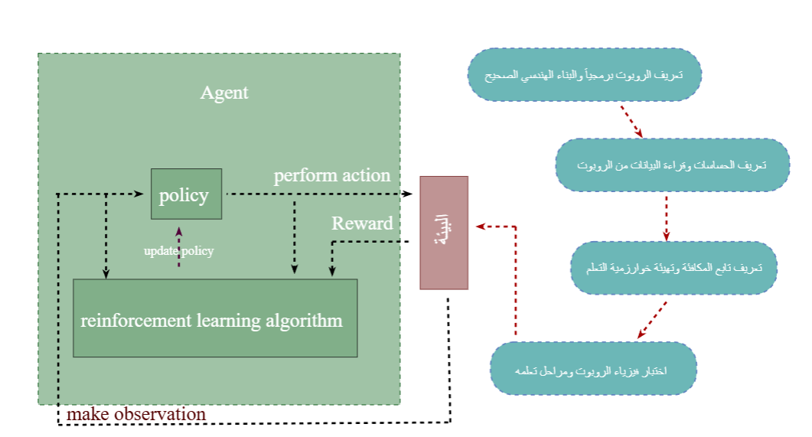
docs/images/rslrl.png
