taimmk/robok-bipedal/docs/images/simulink2.png

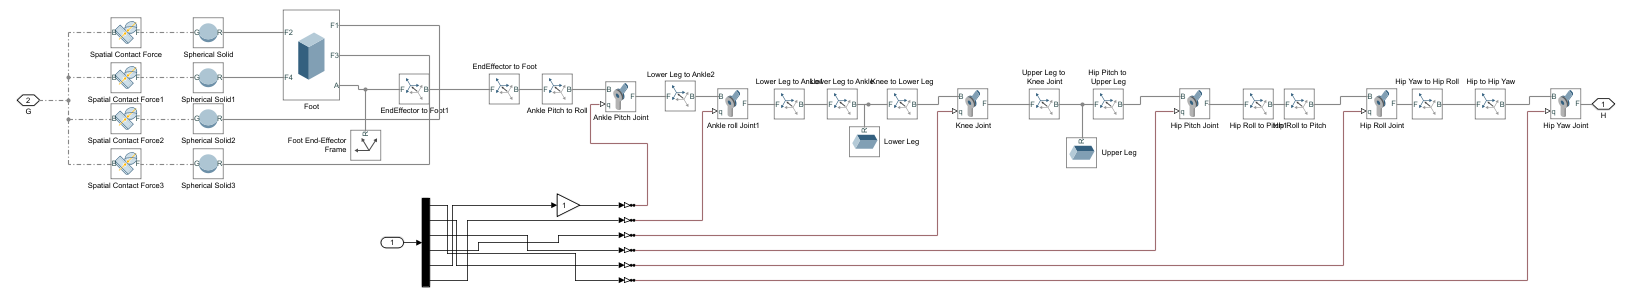
docs/images/simulink2.png
