taimmk/robok-bipedal/docs/images/simulink3dinfo.png

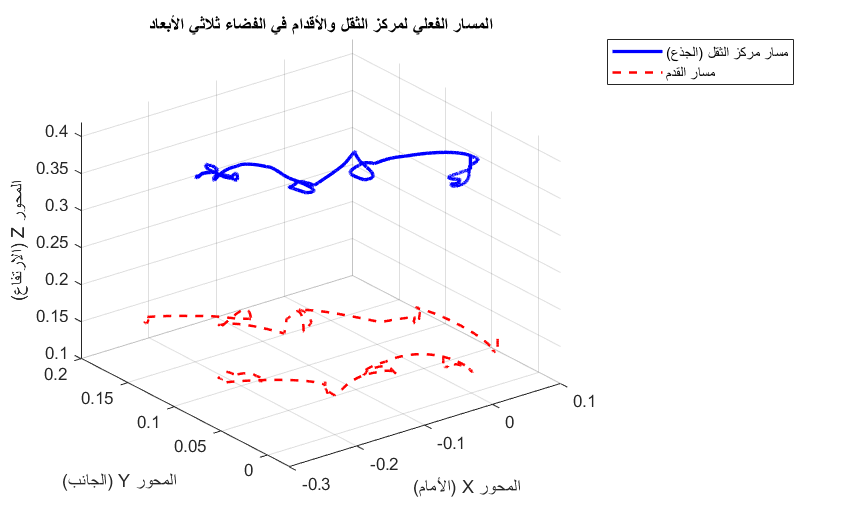
docs/images/simulink3dinfo.png
