taimmk/robok-bipedal/docs/images/simulinkheightinfo.png

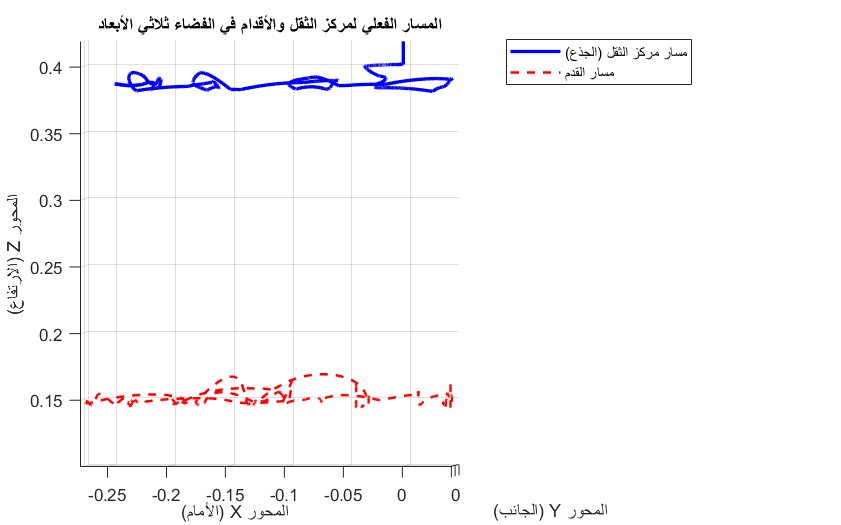
docs/images/simulinkheightinfo.png
