taimmk/robok-bipedal/docs/images/simulinkoutput.png

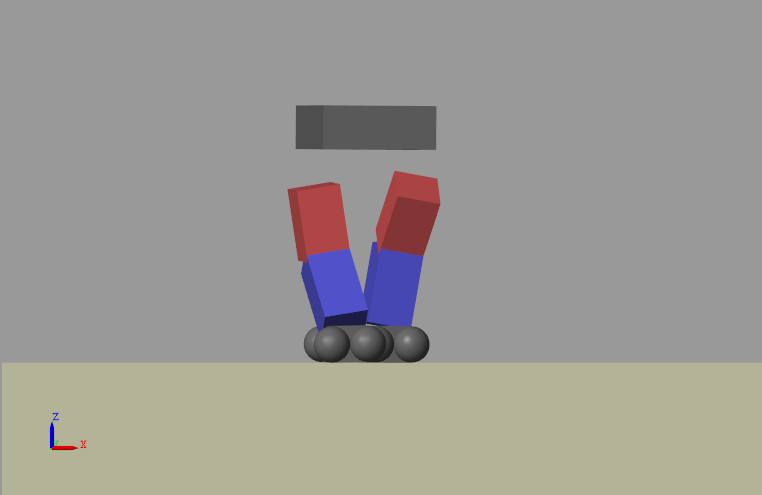
docs/images/simulinkoutput.png
