taimmk/robok-bipedal/docs/images/simulinktopinfo.png

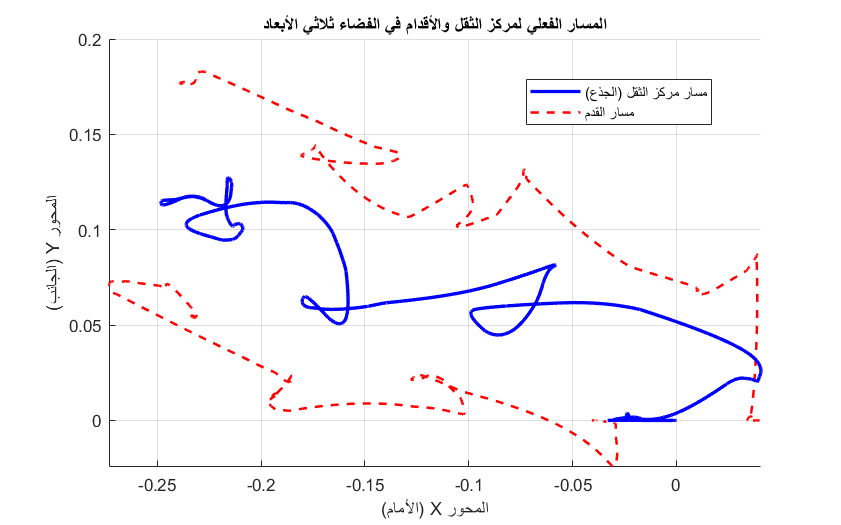
docs/images/simulinktopinfo.png
