taimmk/robok-bipedal/docs/images/torque.png

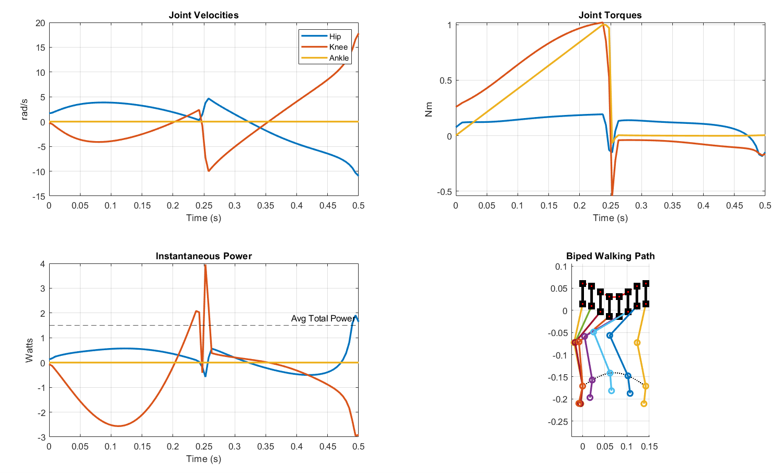
docs/images/torque.png
