taimmk/robok-bipedal/docs/images/walk_cycle.png

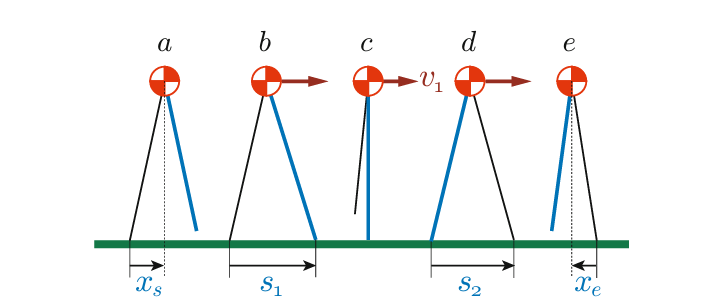
docs/images/walk_cycle.png
