taimmk/robok-bipedal/docs/images/walking_cycle.png

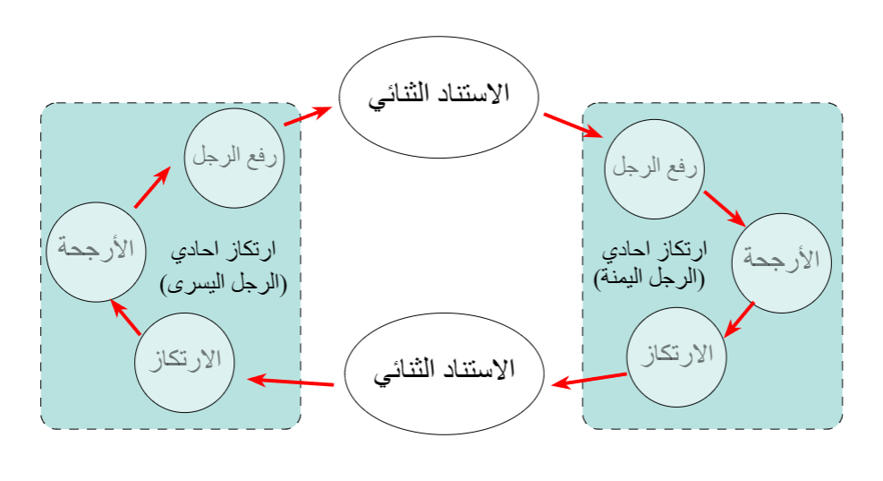
docs/images/walking_cycle.png
