taimmk/robok-bipedal/docs/images/walktraj.png

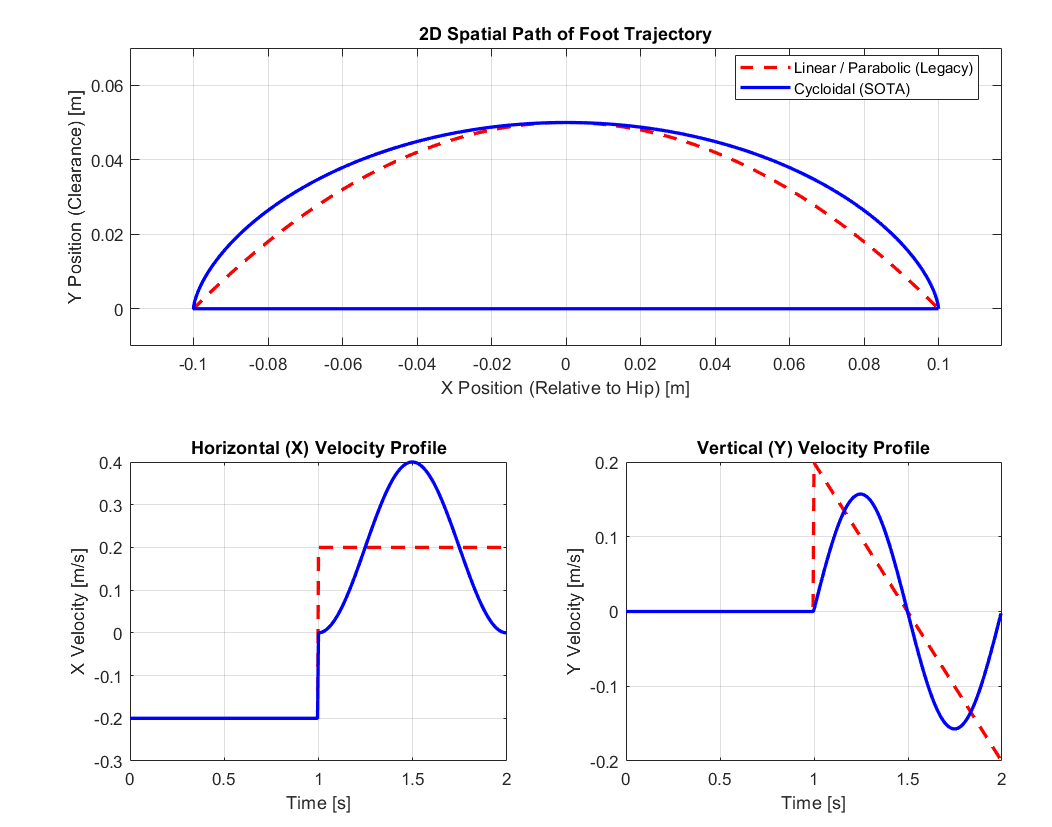
docs/images/walktraj.png
