taimmk/robok-bipedal/docs/images/zmp.png

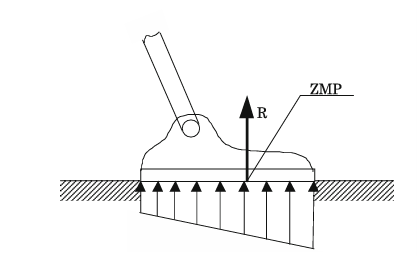
docs/images/zmp.png
