taimmk/robok-bipedal/electrical/pcb/image.png

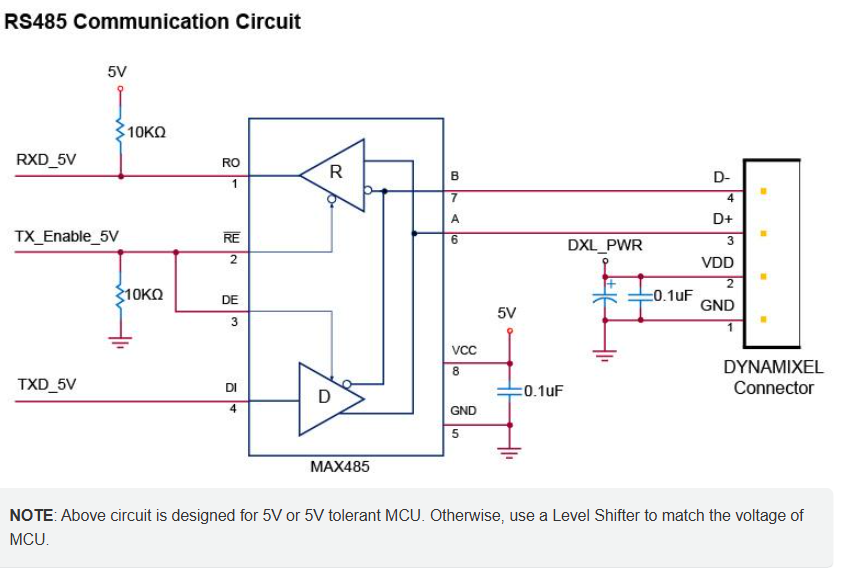
electrical/pcb/image.png
