taimmk/robok-bipedal/electrical/pcb/photo_2026-05-29_12-50-10.jpg

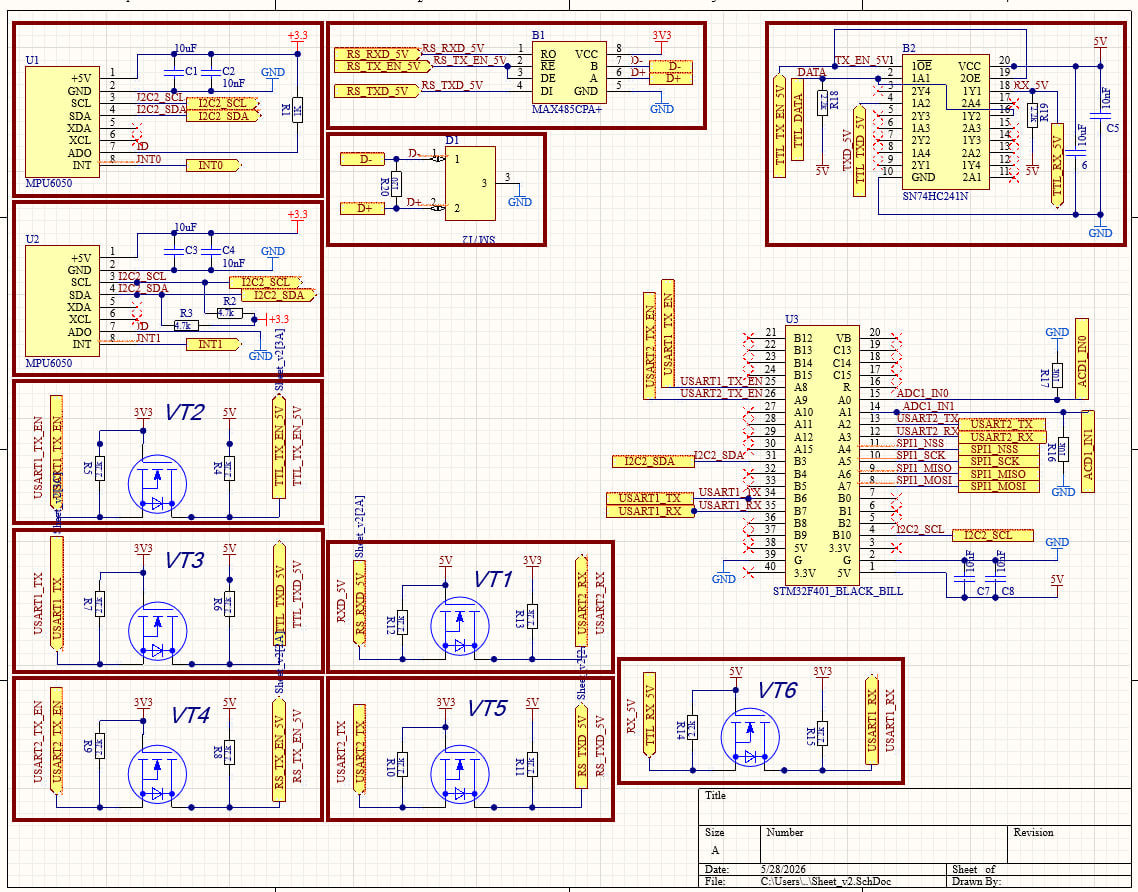
electrical/pcb/photo_2026-05-29_12-50-10.jpg
