taimmk/robok-bipedal/electrical/pcb/Screenshot 2026-05-24 105604.png

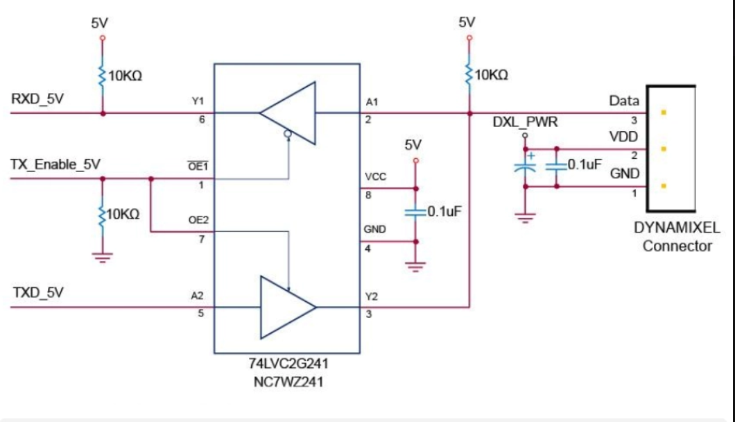
electrical/pcb/Screenshot 2026-05-24 105604.png
