taimmk/robok-bipedal/electrical/pcb/STM32-STM32F4-STM32F401-STM32F401CCU6-pinout-low-resolution-1024x623.jpg

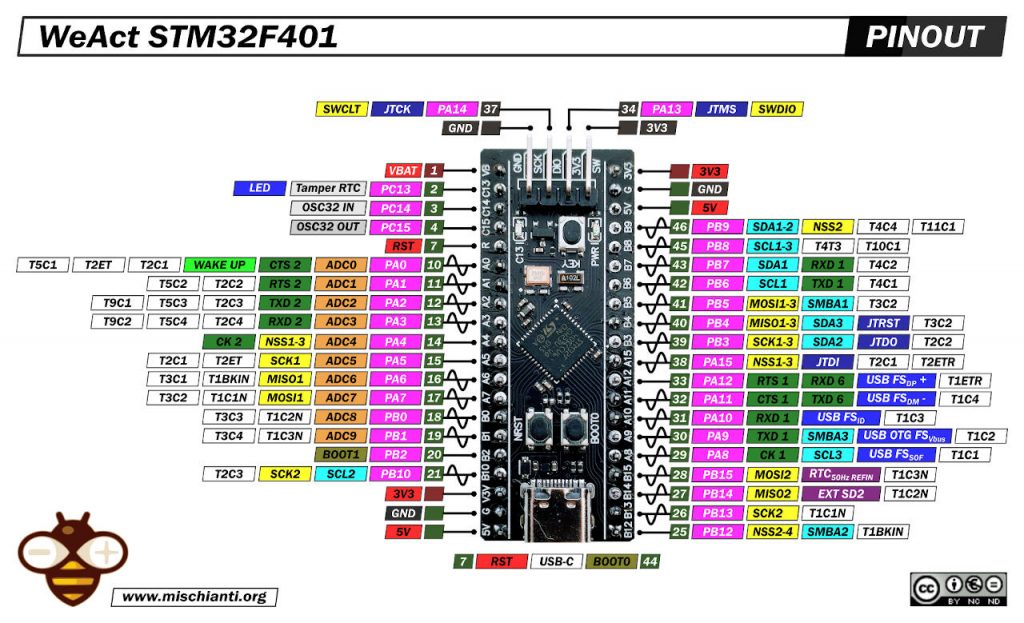
electrical/pcb/STM32-STM32F4-STM32F401-STM32F401CCU6-pinout-low-resolution-1024x623.jpg
