taimmk/robok-bipedal/electrical/pcb/WhatsApp Image 2026-06-11 at 10.53.41.jpeg

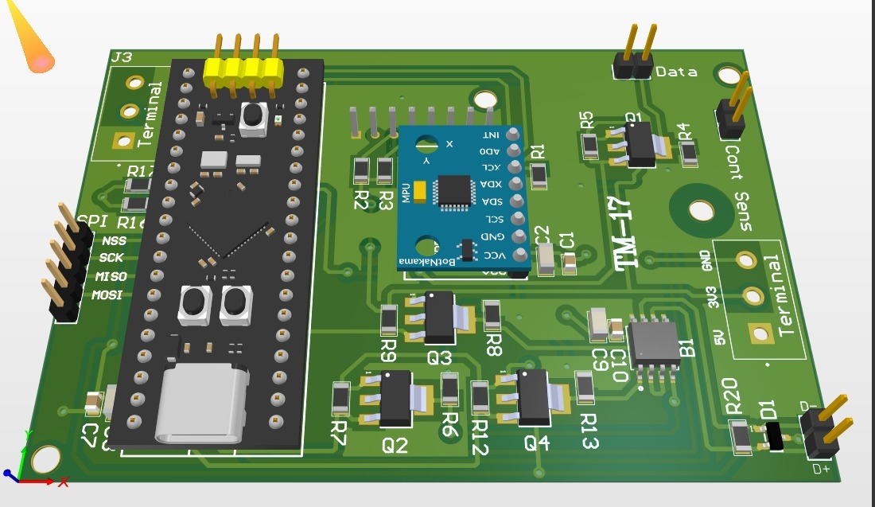
electrical/pcb/WhatsApp Image 2026-06-11 at 10.53.41.jpeg
