taimmk/robok-bipedal/electrical/PCB_RS485_1MB.jpg

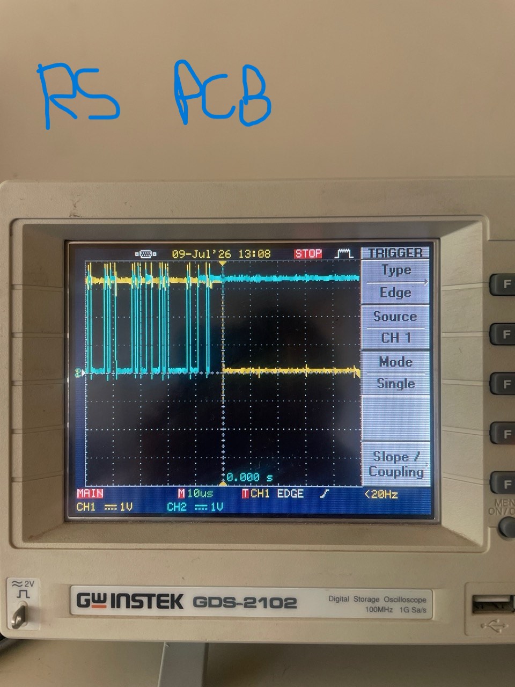
electrical/PCB_RS485_1MB.jpg
