taimmk/robok-bipedal/electrical/PCB_TTL_1MB.jpg

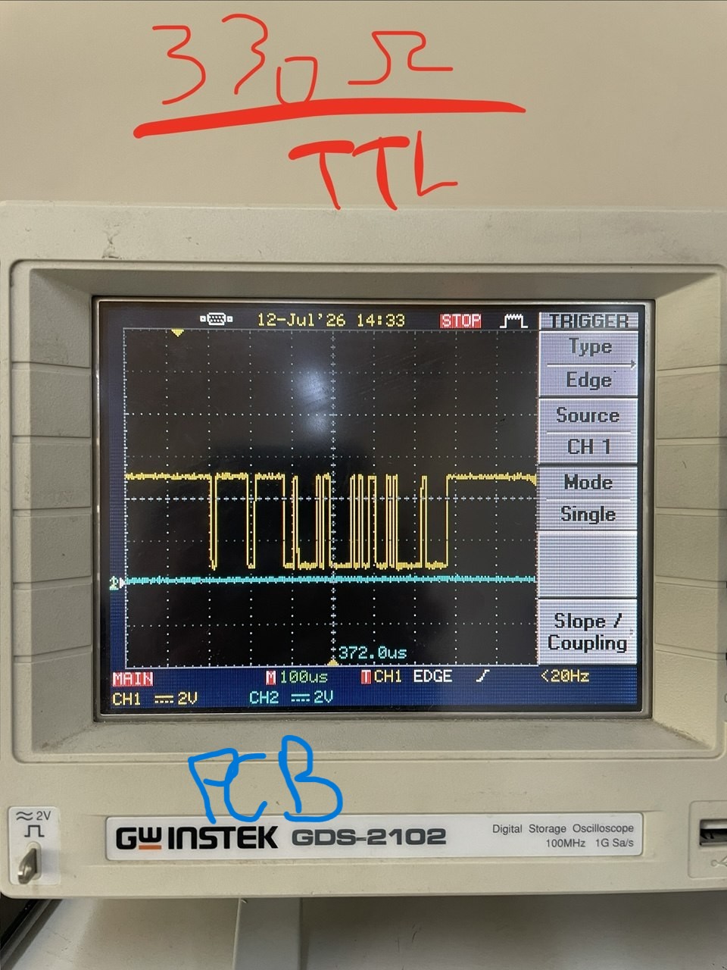
electrical/PCB_TTL_1MB.jpg
