taimmk/robok-bipedal/docs/images/ANSYS/foot_setup.png

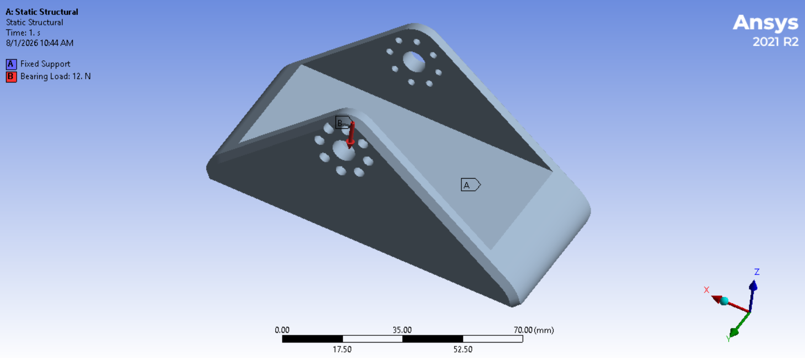
docs/images/ANSYS/foot_setup.png
