taimmk/robok-bipedal/docs/images/ANSYS/linkii_setup.png

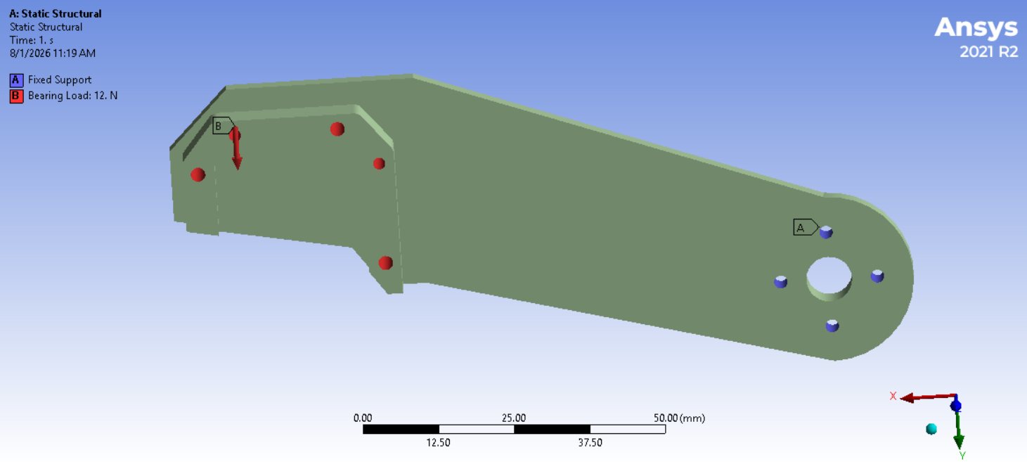
docs/images/ANSYS/linkii_setup.png
