taimmk/robok-bipedal/docs/images/ANSYS/nick_setup.png

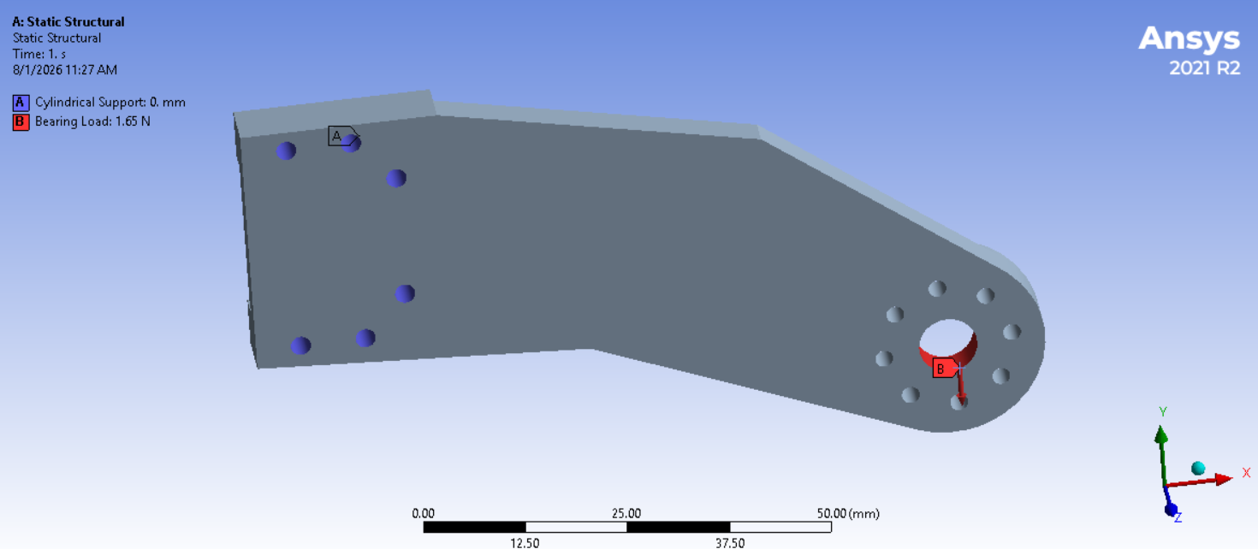
docs/images/ANSYS/nick_setup.png
