taimmk/robok-bipedal/docs/images/simulinksetup.png

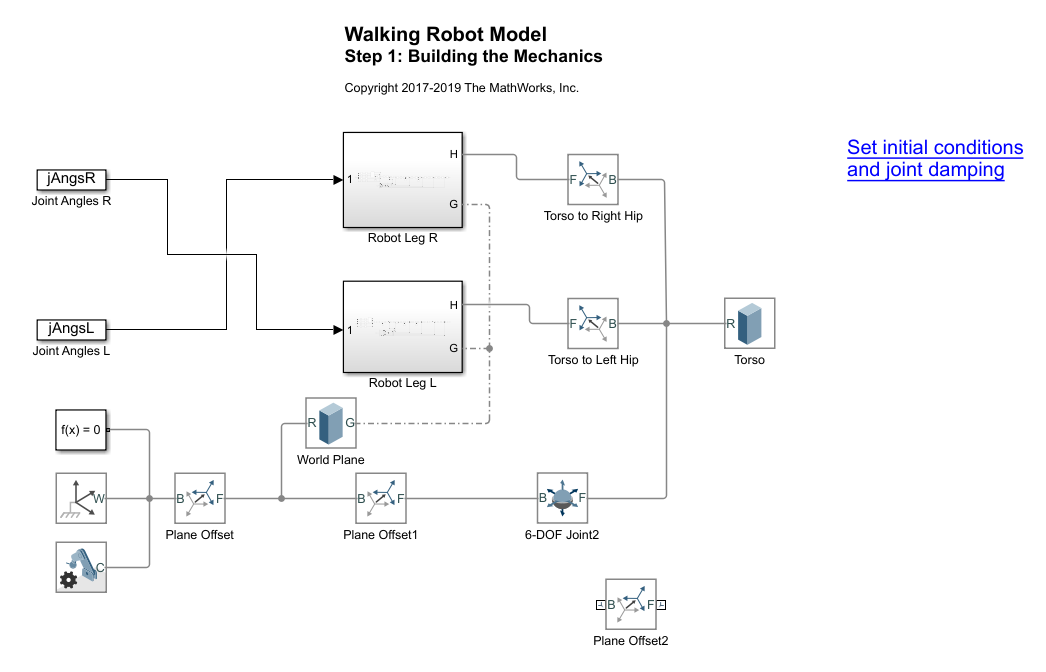
docs/images/simulinksetup.png
