taimmk/robok-bipedal/electrical/TESTBOARD_RS485_115KB.jpg

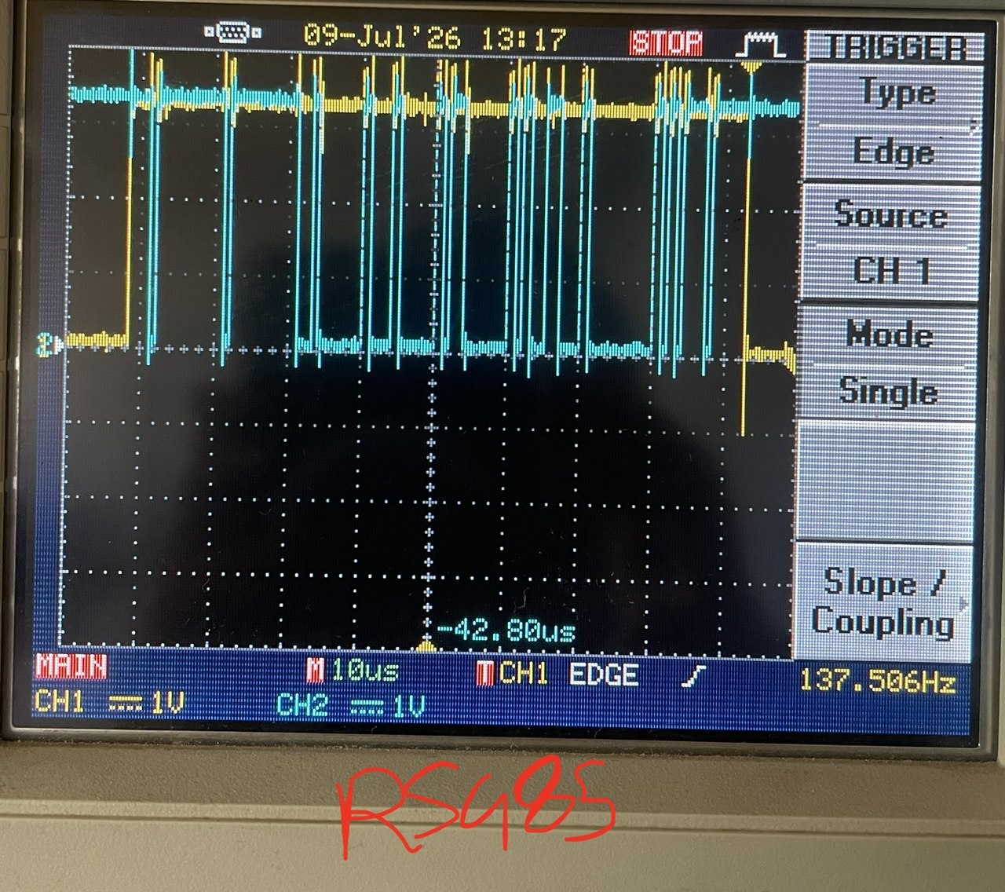
electrical/TESTBOARD_RS485_115KB.jpg
