taimmk/robok-bipedal/electrical/TESTBOARD_TTL_1MB.jpg

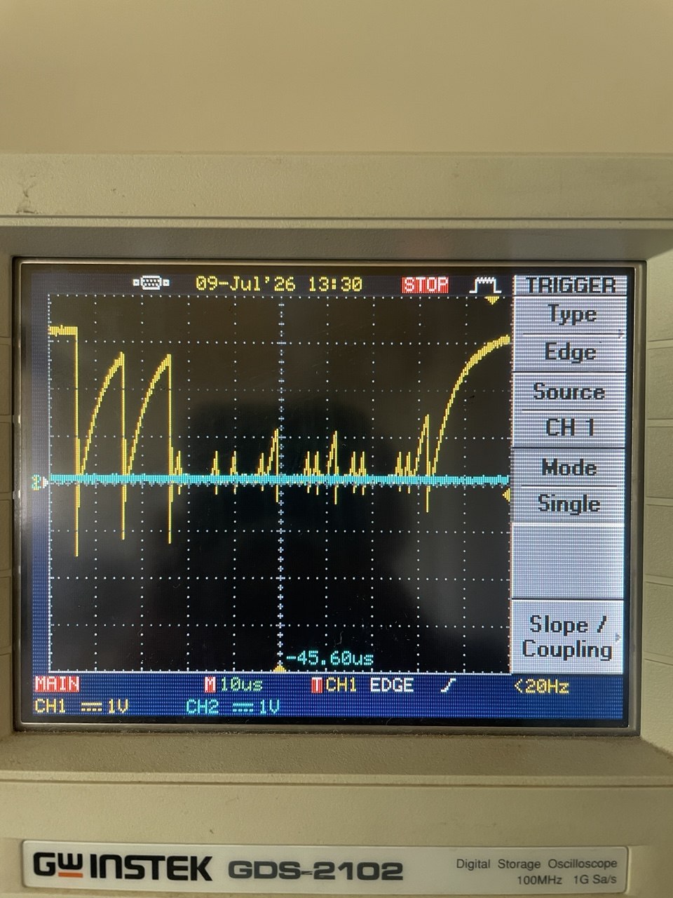
electrical/TESTBOARD_TTL_1MB.jpg
