taimmk/robok-bipedal/electrical/TESTBOARD_TTL_115KB.jpg

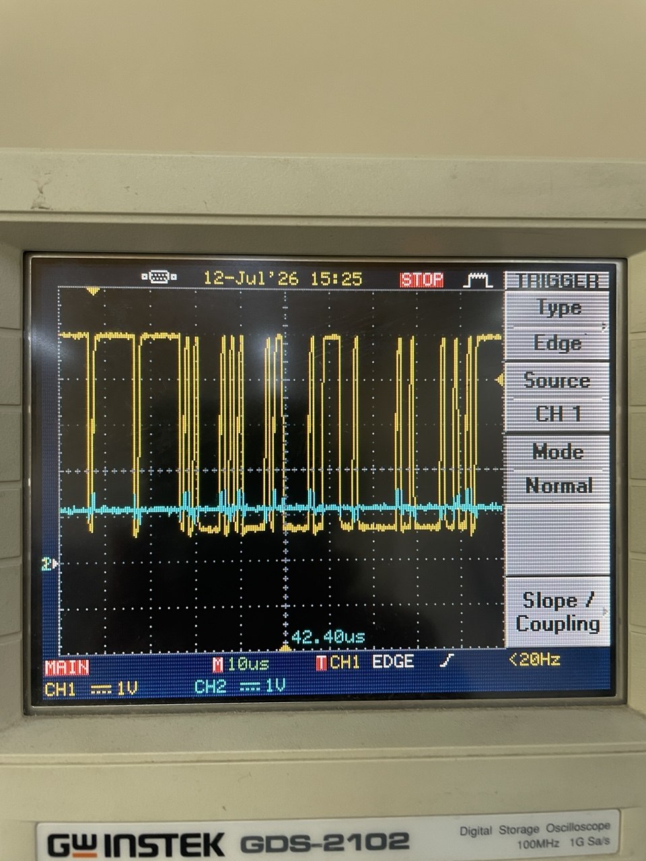
electrical/TESTBOARD_TTL_115KB.jpg
