taimmk/robok-bipedal/electrical/TESTBOARD_TTL_500KB.jpg

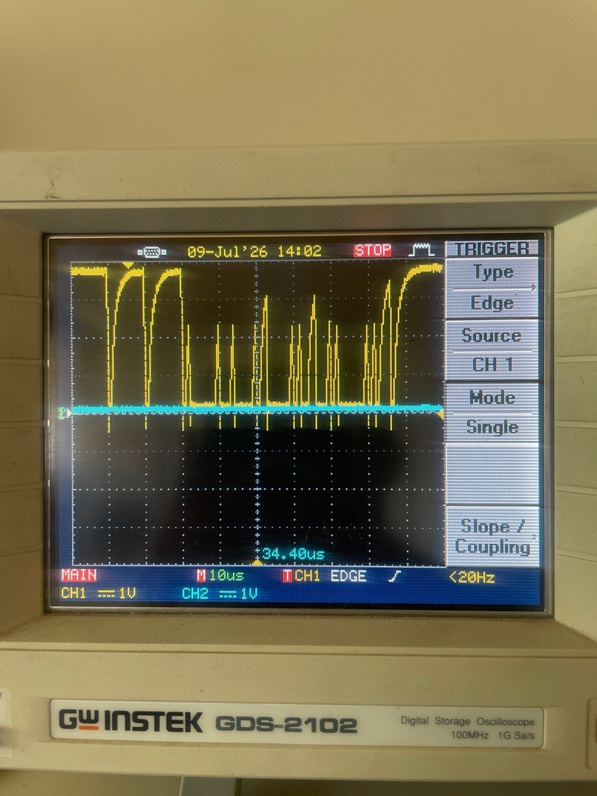
electrical/TESTBOARD_TTL_500KB.jpg
