taimmk/robok-bipedal/results/videos/RS485 test board 150kbps.jpg

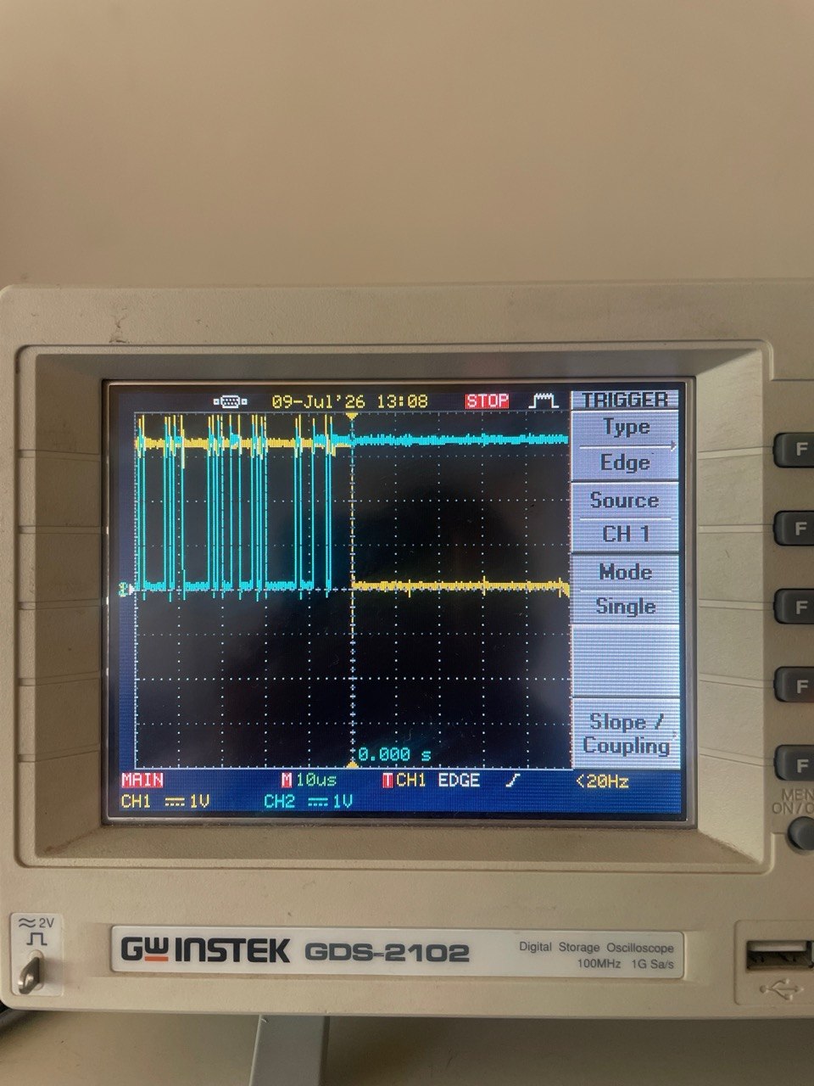
results/videos/RS485 test board 150kbps.jpg
